ZemanNz/ESP-Demo-Box/documentation/barevny.png

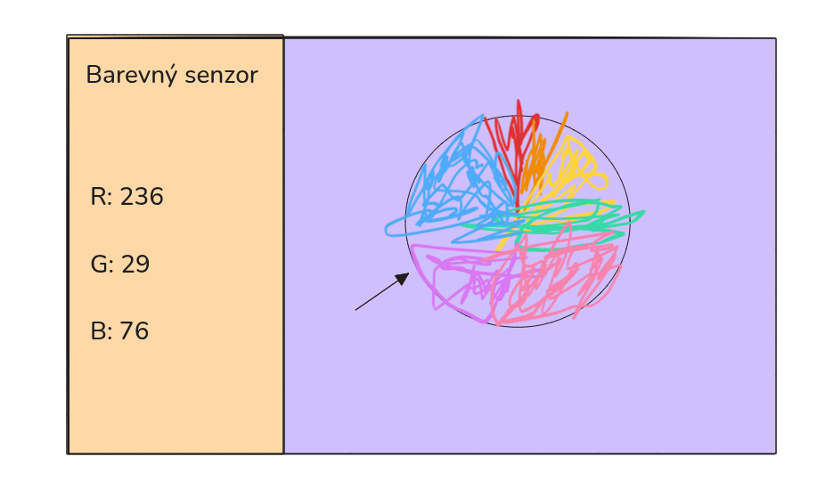
documentation/barevny.png
