ZemanNz/ESP-Demo-Box/documentation/IMG_20260813_224419984.jpg

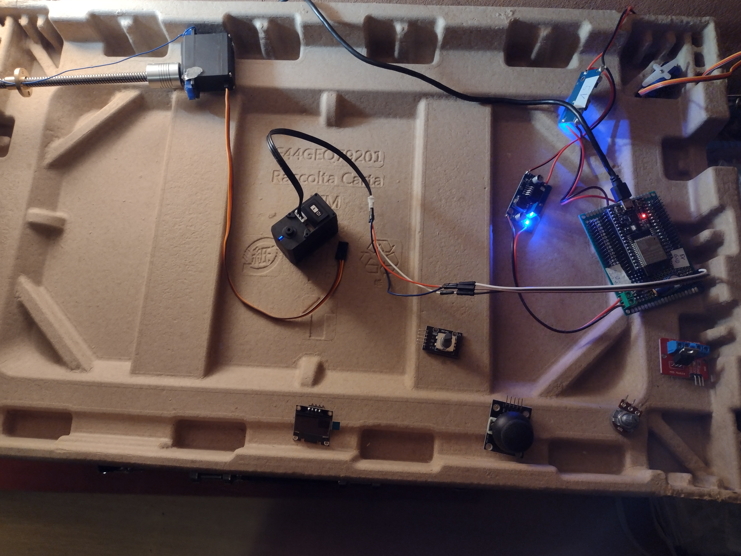
documentation/IMG_20260813_224419984.jpg
