ZemanNz/ESP-Demo-Box/documentation/plan_mode_main_menu.png

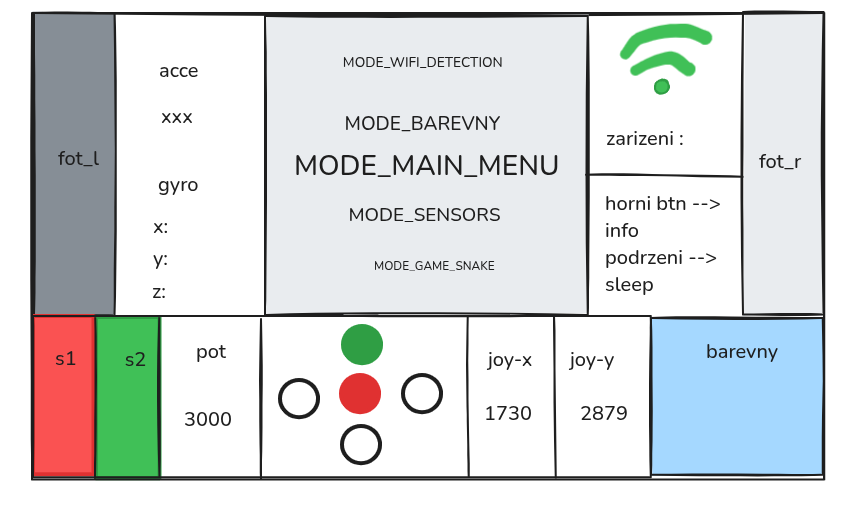
documentation/plan_mode_main_menu.png
