ZemanNz/ESP-Demo-Box/documentation/Snímek obrazovky z 2026-07-06 16-27-45.png

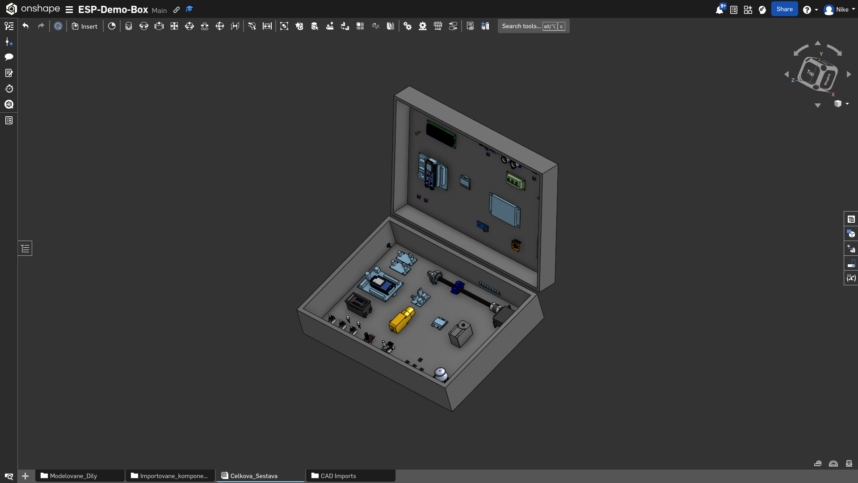
documentation/Snímek obrazovky z 2026-07-06 16-27-45.png
