ZemanNz/ESP-Demo-Box/documentation/Snímek obrazovky z 2026-07-15 17-25-52.png

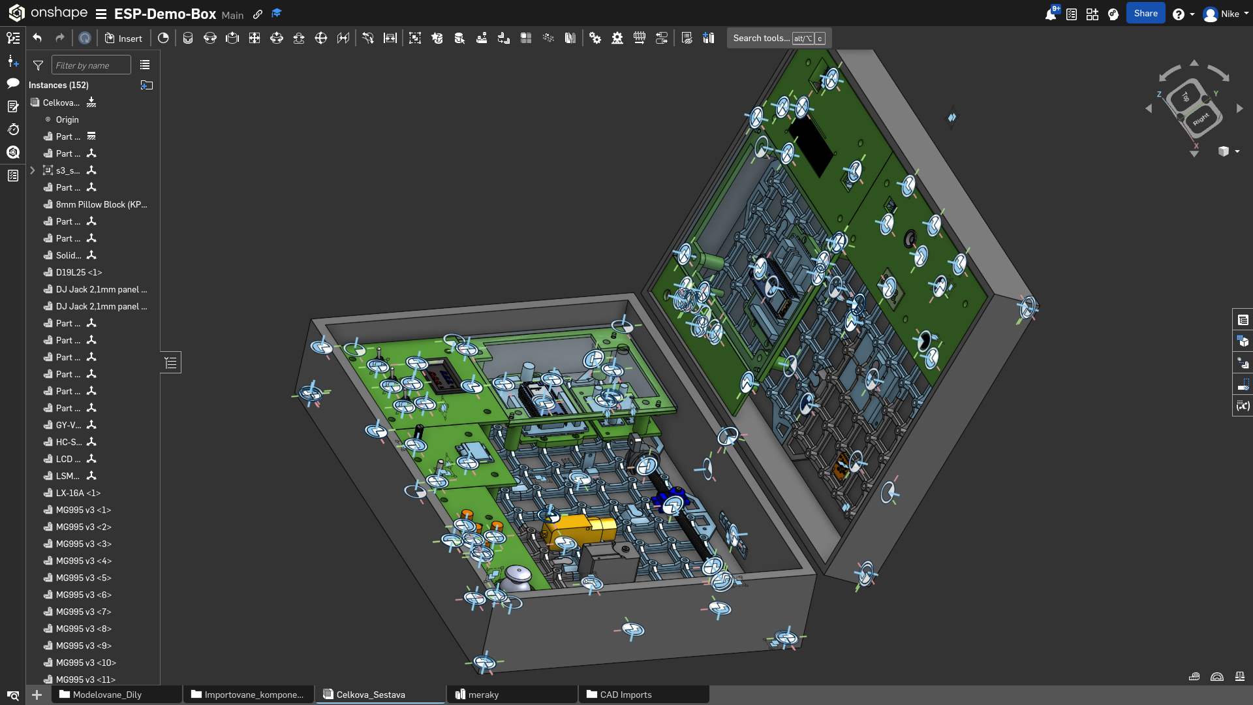
documentation/Snímek obrazovky z 2026-07-15 17-25-52.png
