ZemanNz/ESP-Demo-Box/documentation/Snímek obrazovky z 2026-08-08 21-47-14.png

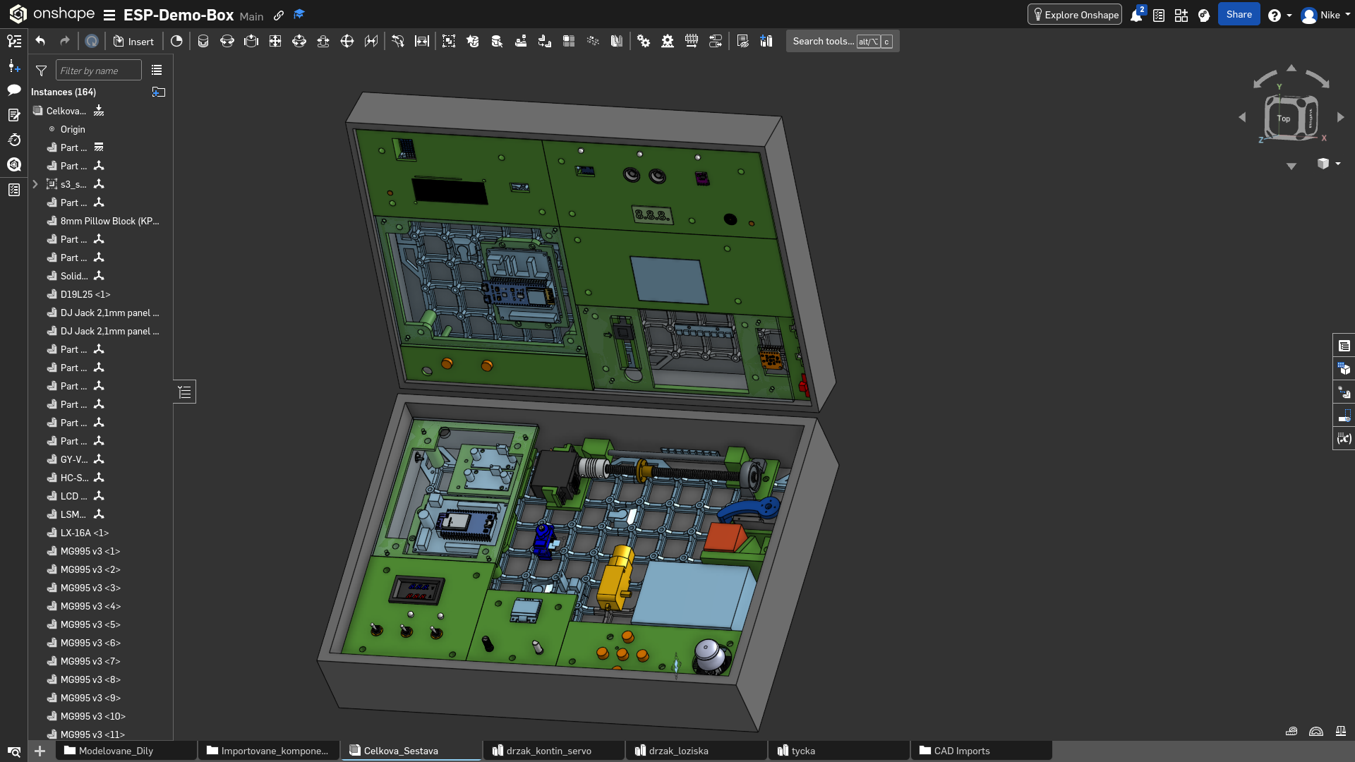
documentation/Snímek obrazovky z 2026-08-08 21-47-14.png
