ZemanNz/ESP-Demo-Box/documentation/Snímek obrazovky z 2026-08-09 14-38-35.png

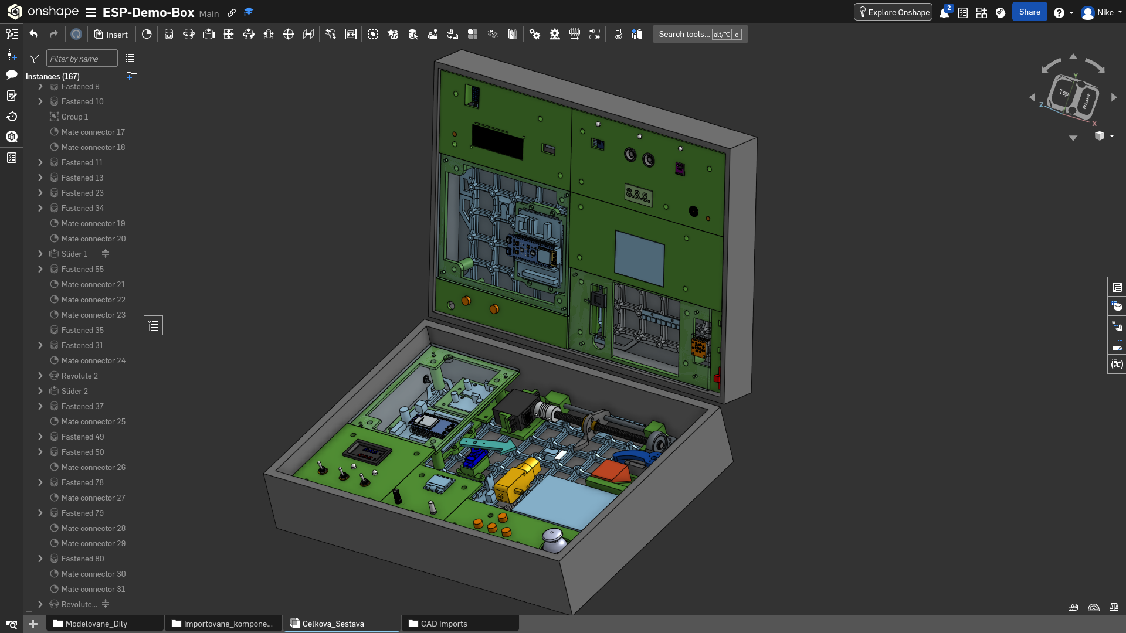
documentation/Snímek obrazovky z 2026-08-09 14-38-35.png
