ZemanNz/ESP-Demo-Box/documentation/vzdalenost.png

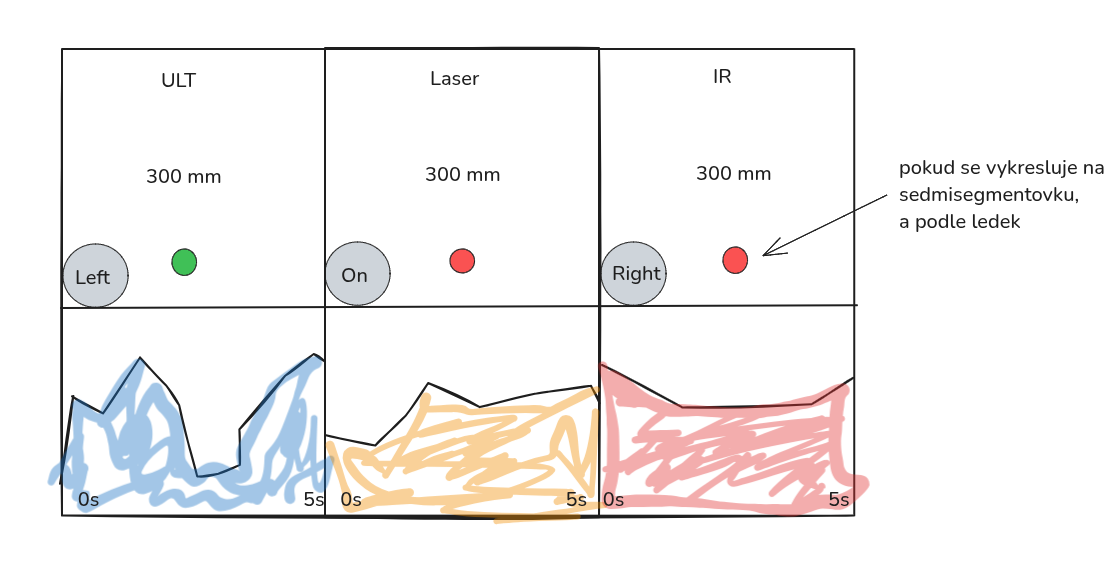
documentation/vzdalenost.png
