ZemanNz/ESP-Demo-Box/documentation/zapojeni_celkem.png

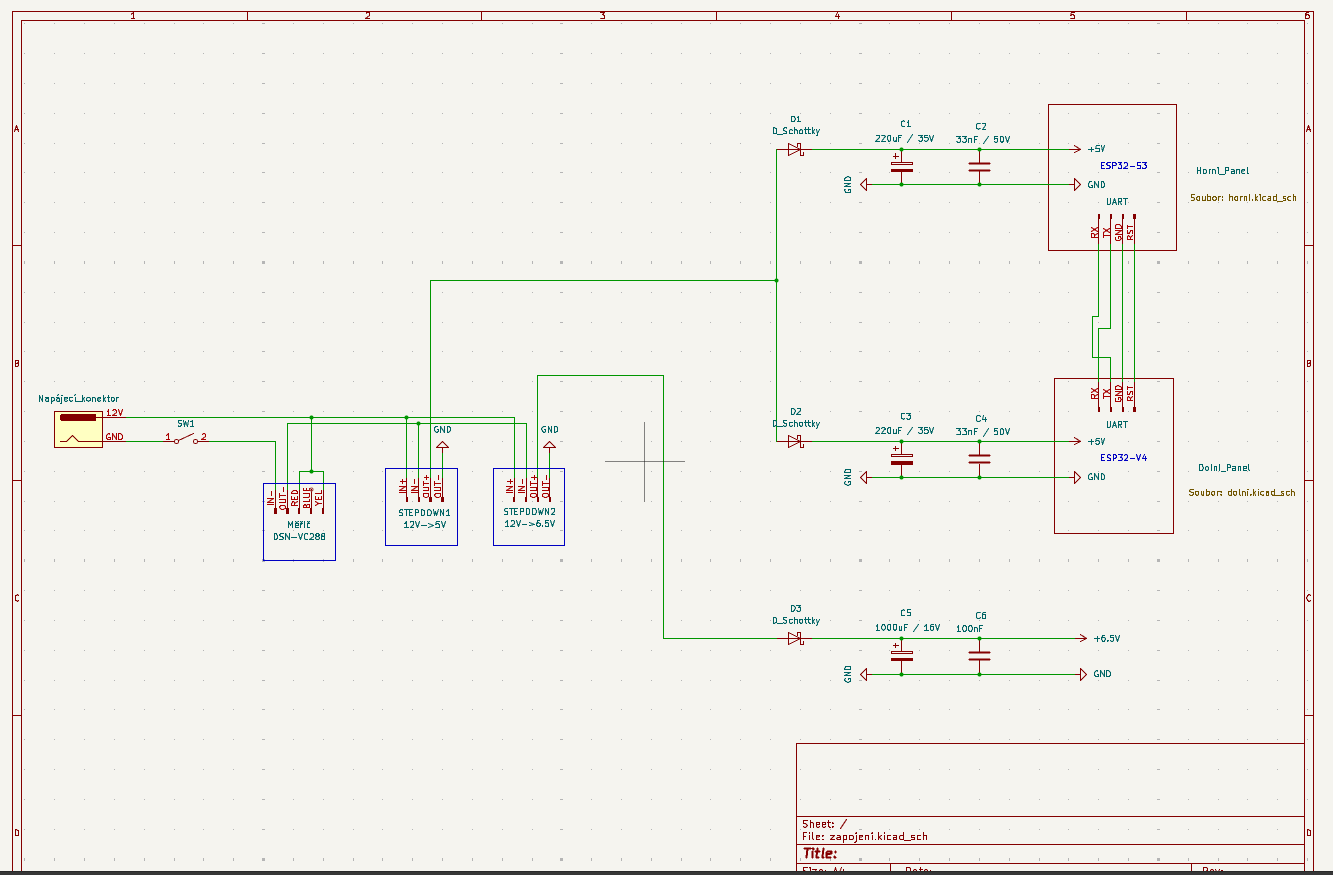
documentation/zapojeni_celkem.png
