ZemanNz/ESP-Demo-Box/documentation/zapojeni_dolni.png

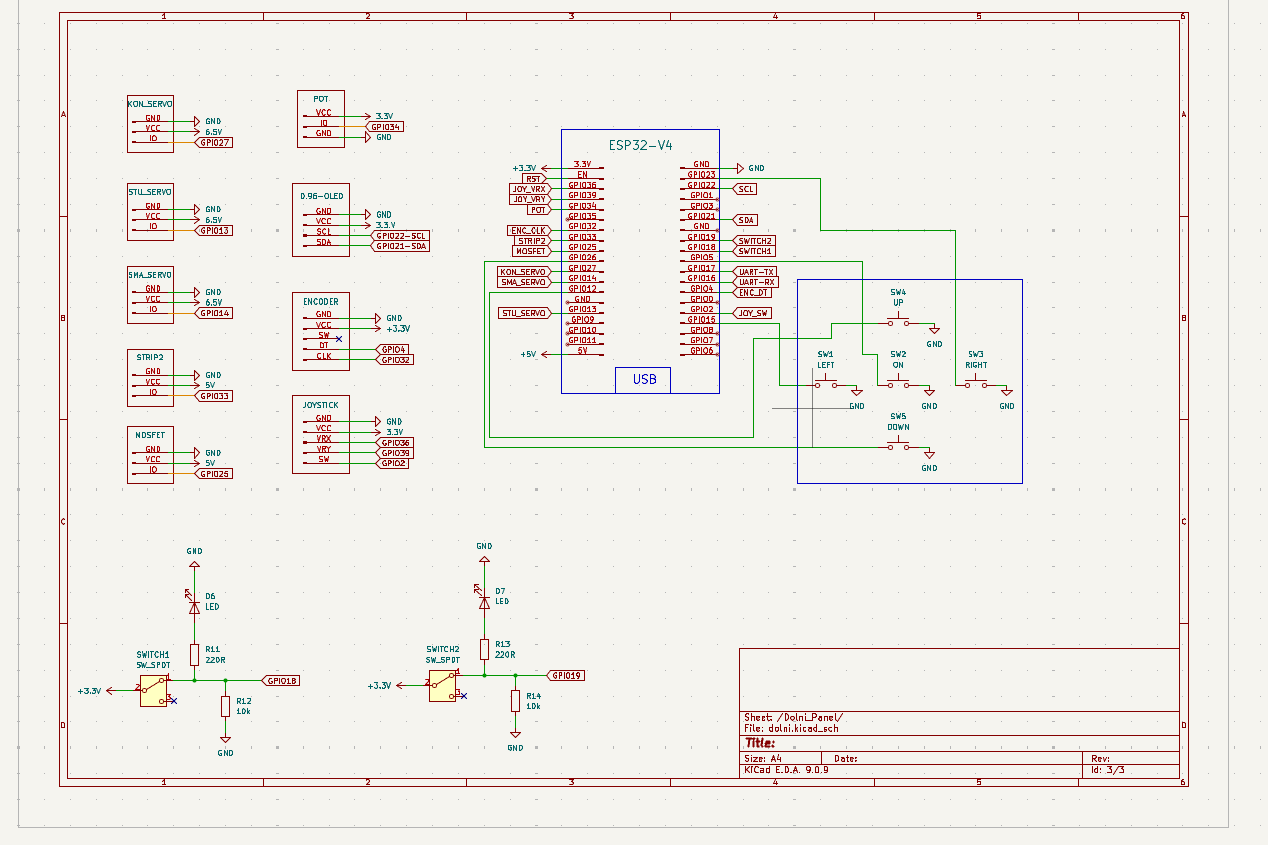
documentation/zapojeni_dolni.png
