ZemanNz/ESP-Demo-Box/hardware/3D/modelovane/drzak_dolni/drzak_dolni_4.step

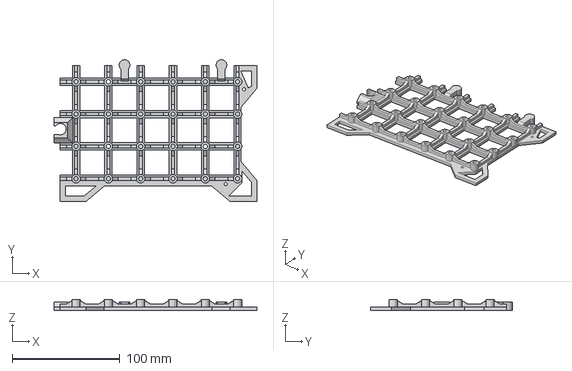
[picture p34: CAD file, 2026-07-23]
hardware/3D/modelovane/drzak_dolni/drzak_dolni_4.step
188.5 x 131.5 x 10.0 mm
