ZemanNz/ESP-Demo-Box/hardware/3D/modelovane/drzak_loziska.step

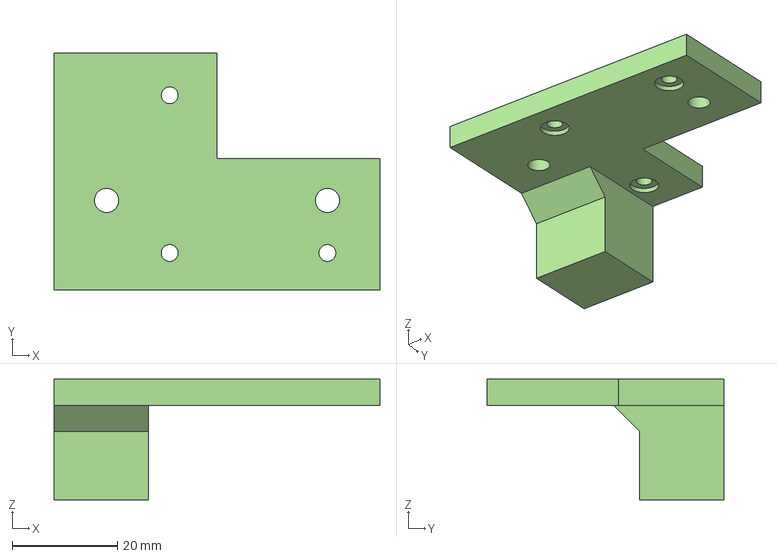
[picture p35: CAD file, 2026-09-20]
hardware/3D/modelovane/drzak_loziska.step
62.0 x 45.0 x 23.0 mm
