ZemanNz/ESP-Demo-Box/hardware/3D/LM2596S_Y000022.step

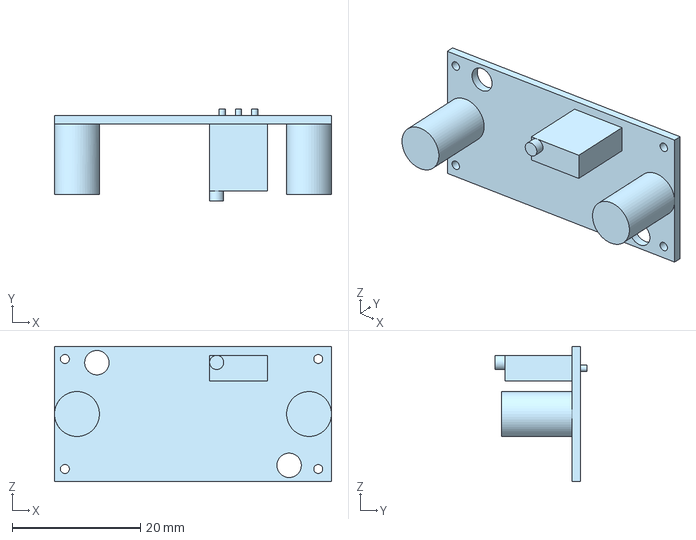
[picture p36: CAD file, 2026-07-23]
hardware/3D/LM2596S_Y000022.step
43.2 x 14.3 x 21.1 mm
