ZemanNz/ESP-Demo-Box/hardware/3D/modelovane/drzak_kontin_servo.step

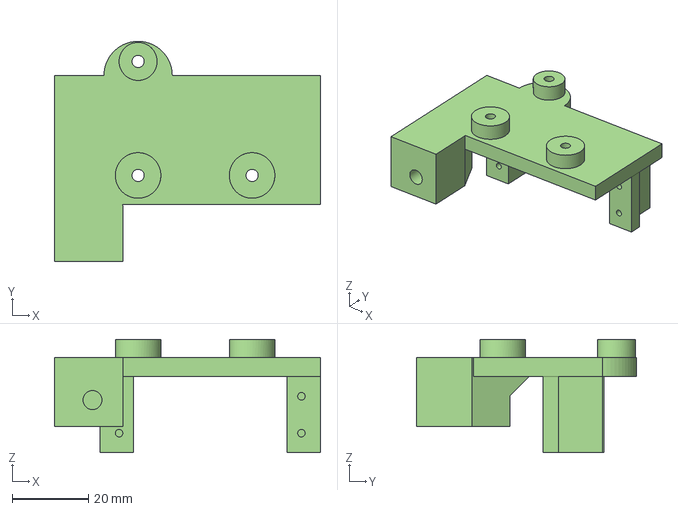
[picture p37: CAD file, 2026-09-20]
hardware/3D/modelovane/drzak_kontin_servo.step
70.0 x 58.0 x 29.9 mm
