ZemanNz/ESP-Demo-Box/hardware/3D/dc 022B jack 2.1mm.step

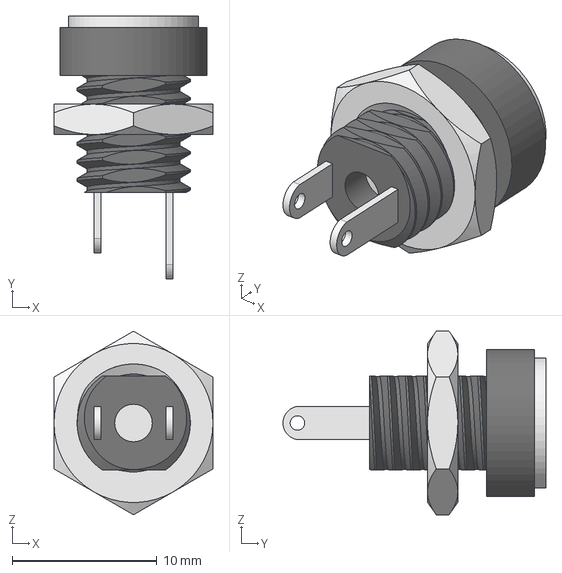
[picture p38: CAD file, 2026-07-23]
hardware/3D/dc 022B jack 2.1mm.step
11.0 x 18.2 x 12.7 mm
