ZemanNz/ESP-Demo-Box/hardware/3D/modelovane/drzak_9g.step

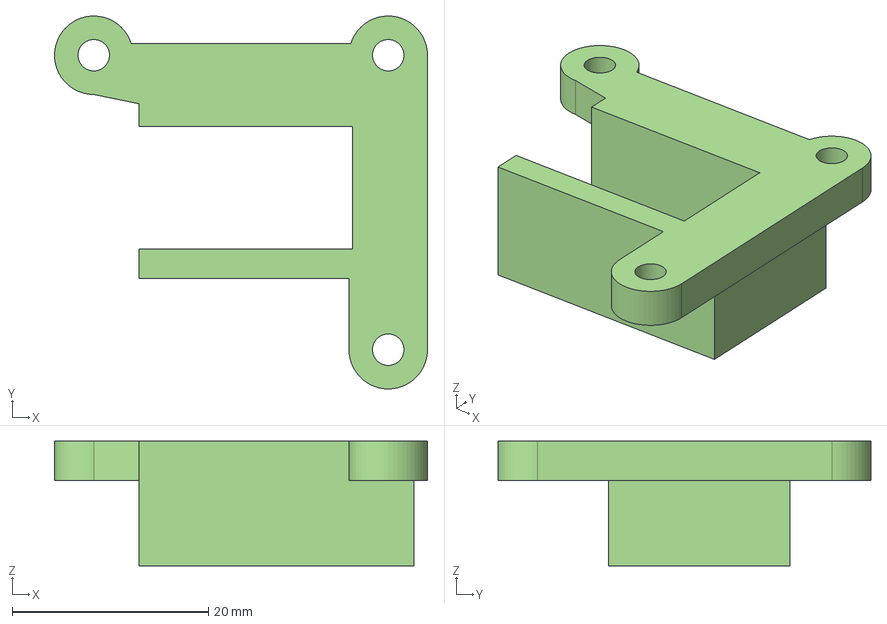
[picture p39: CAD file, 2026-09-20]
hardware/3D/modelovane/drzak_9g.step
38.0 x 38.0 x 12.7 mm
