ZemanNz/ESP-Demo-Box/hardware/3D/modelovane/nad_joy.step

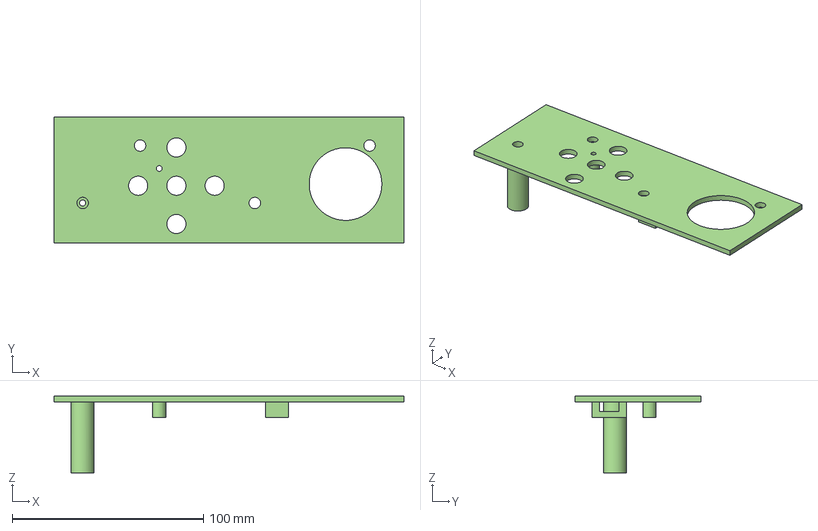
[picture p40: CAD file, 2026-08-15]
hardware/3D/modelovane/nad_joy.step
183.0 x 66.0 x 40.0 mm
