ZemanNz/ESP-Demo-Box/hardware/3D/MTS-102-switch.step

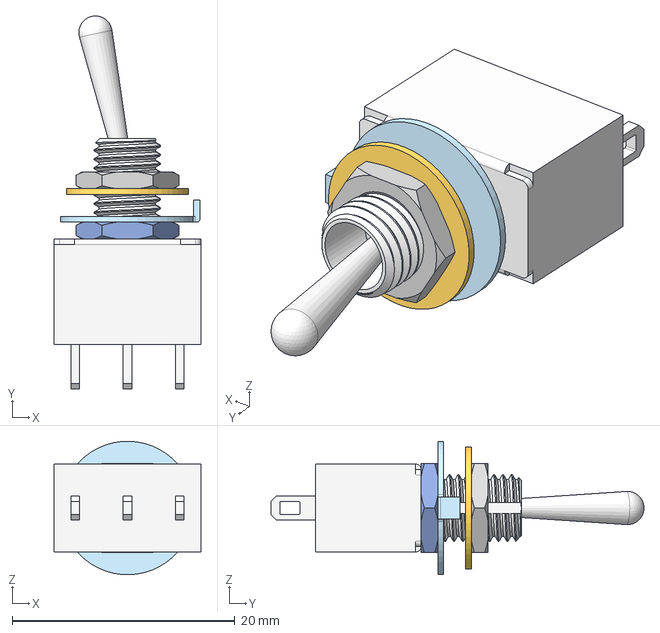
[picture p41: CAD file, 2026-07-23]
hardware/3D/MTS-102-switch.step
13.2 x 33.5 x 12.0 mm
