ZemanNz/ESP-Demo-Box/hardware/3D/modelovane/drzak_joy.step

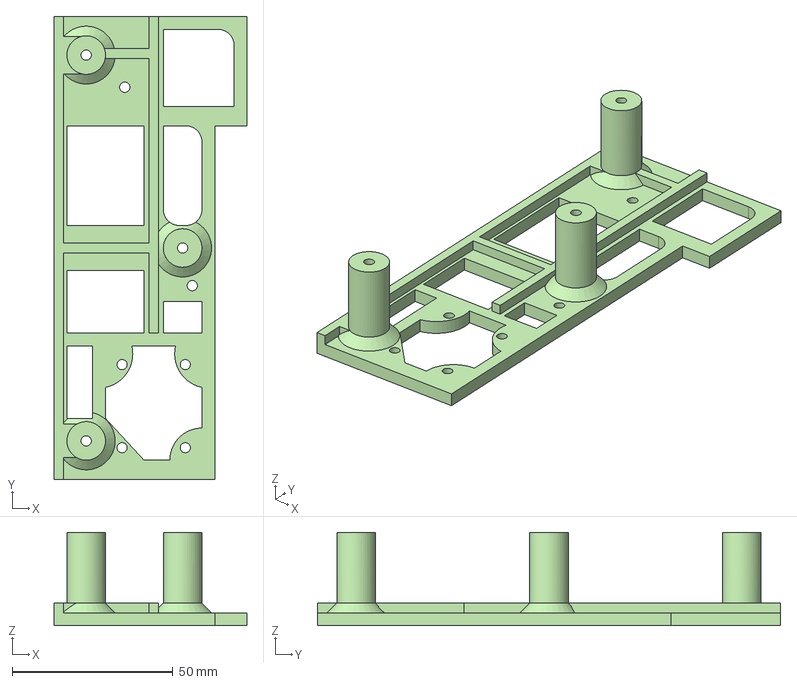
[picture p42: CAD file, 2026-08-15]
hardware/3D/modelovane/drzak_joy.step
60.0 x 144.0 x 29.0 mm
