ZemanNz/ESP-Demo-Box/hardware/3D/HW-040.step

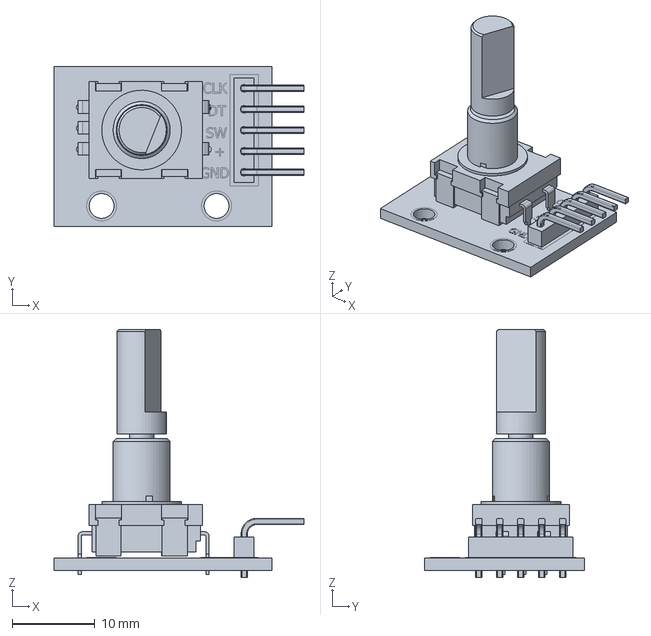
[picture p43: CAD file, 2026-07-23]
hardware/3D/HW-040.step
30.3 x 19.3 x 30.1 mm
