ZemanNz/ESP-Demo-Box/hardware/3D/modelovane/nad_reset.step

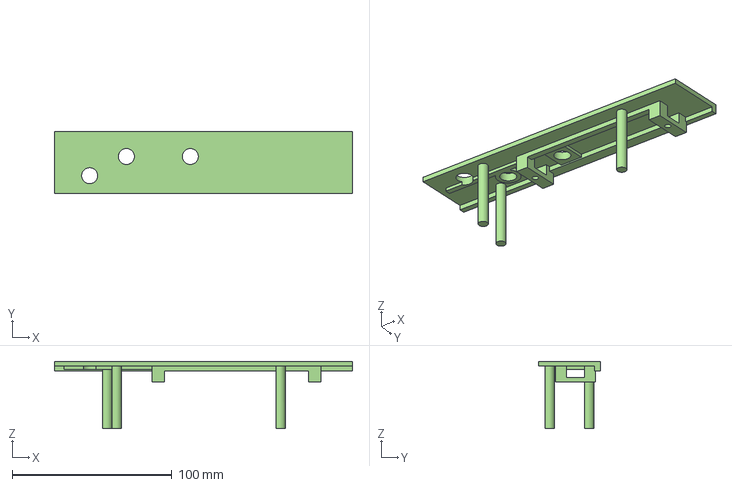
[picture p44: CAD file, 2026-07-23]
hardware/3D/modelovane/nad_reset.step
186.5 x 38.5 x 42.0 mm
