ZemanNz/ESP-Demo-Box/hardware/3D/Joystick Module.step

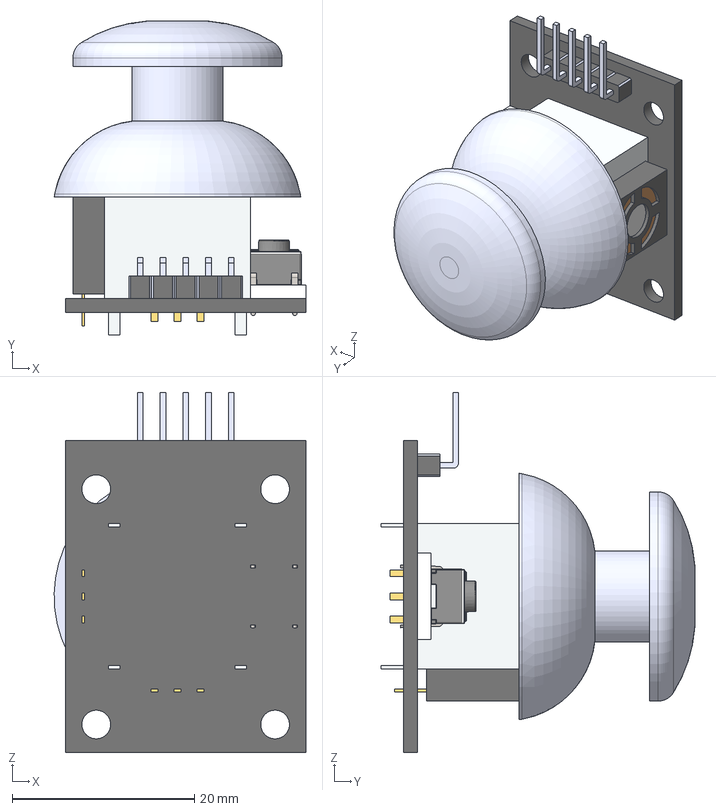
[picture p45: CAD file, 2026-07-23]
hardware/3D/Joystick Module.step
27.6 x 34.5 x 39.5 mm
