ZemanNz/ESP-Demo-Box/hardware/3D/modelovane/drzak_plex_s3.step

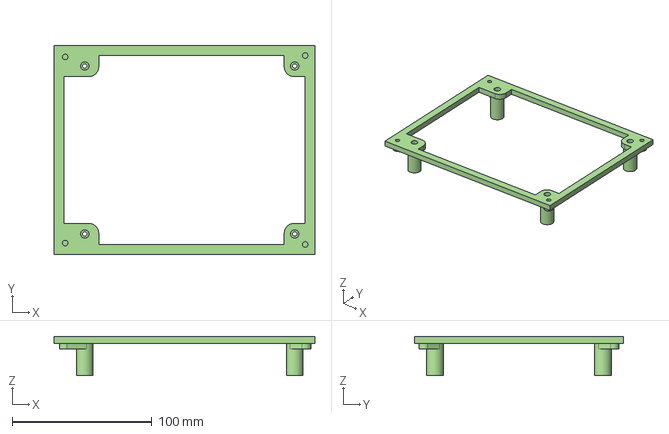
[picture p46: CAD file, 2026-07-23]
hardware/3D/modelovane/drzak_plex_s3.step
186.5 x 149.0 x 28.0 mm
