ZemanNz/ESP-Demo-Box/hardware/3D/DSN-VC288.step

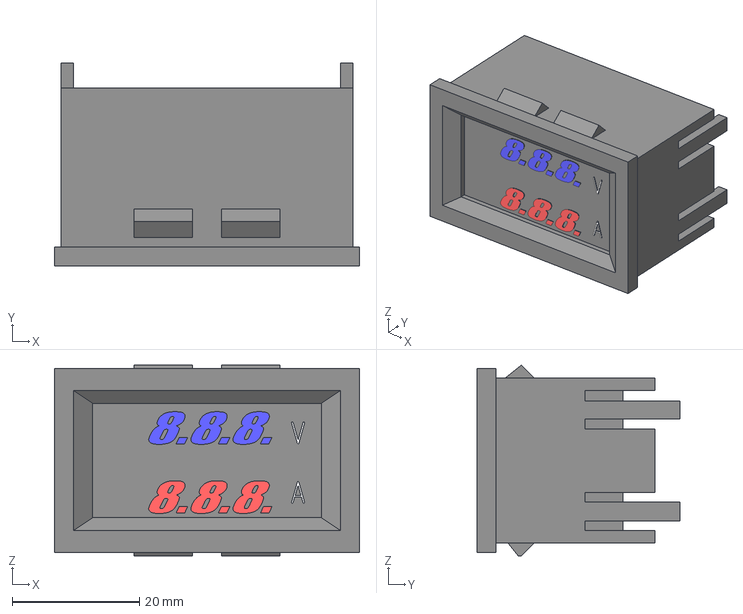
[picture p47: CAD file, 2026-07-23]
hardware/3D/DSN-VC288.step
48.0 x 32.0 x 30.0 mm
