ZemanNz/ESP-Demo-Box/hardware/3D/modelovane/cudlik.step

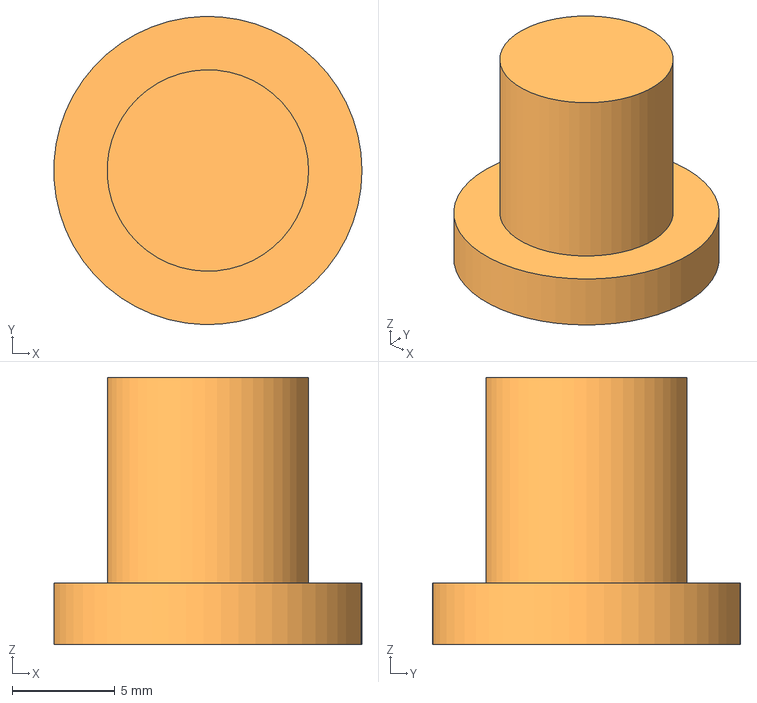
[picture p48: CAD file, 2026-07-23]
hardware/3D/modelovane/cudlik.step
15.0 x 15.0 x 13.0 mm
