ZemanNz/ESP-Demo-Box/hardware/3D/modelovane/barenej_drzak.step

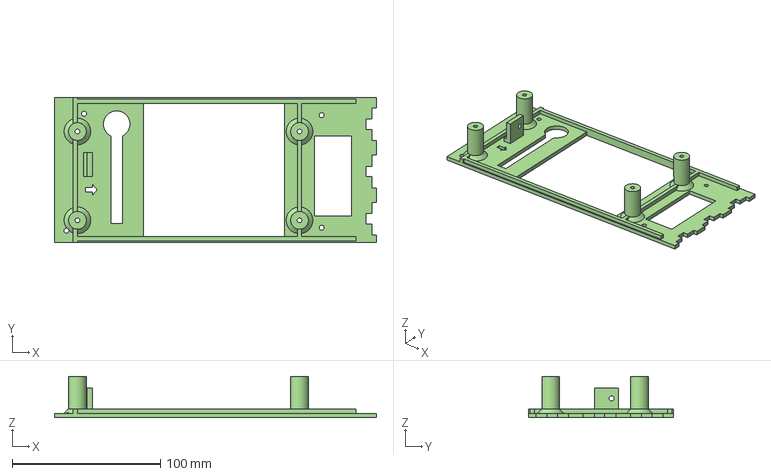
[picture p49: CAD file, 2026-07-23]
hardware/3D/modelovane/barenej_drzak.step
217.5 x 98.0 x 28.0 mm
