ZemanNz/ESP-Demo-Box/hardware/3D/MOS Module.step

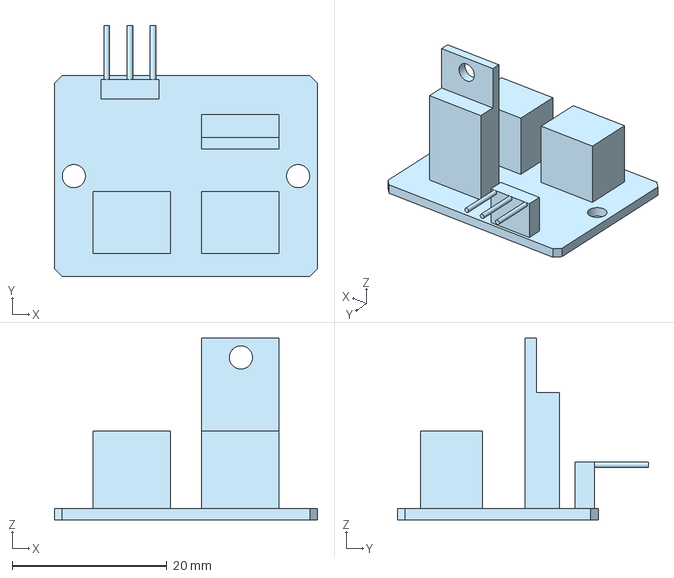
[picture p50: CAD file, 2026-07-23]
hardware/3D/MOS Module.step
34.0 x 32.5 x 23.5 mm
