ZemanNz/ESP-Demo-Box/hardware/3D/GY-VL53LDK.step

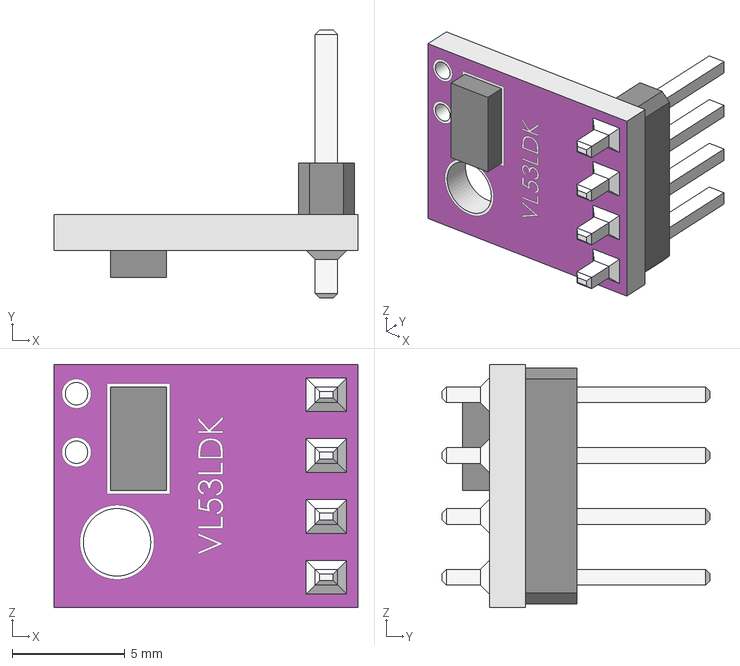
[picture p51: CAD file, 2026-07-23]
hardware/3D/GY-VL53LDK.step
13.5 x 11.9 x 10.8 mm
