ZemanNz/ESP-Demo-Box/hardware/3D/modelovane/drzak_switch.step

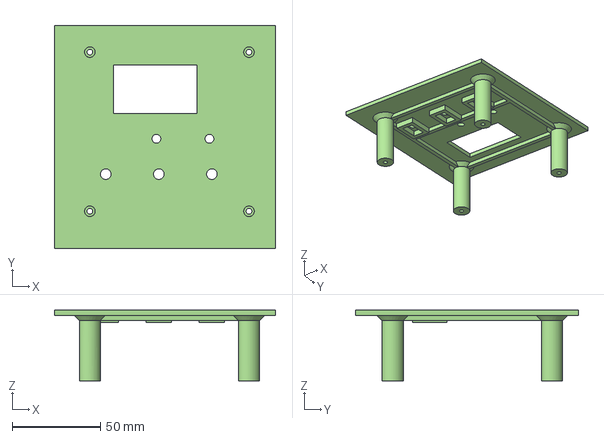
[picture p52: CAD file, 2026-07-23]
hardware/3D/modelovane/drzak_switch.step
125.0 x 126.0 x 40.0 mm
