ZemanNz/ESP-Demo-Box/hardware/3D/HC-SR04.step

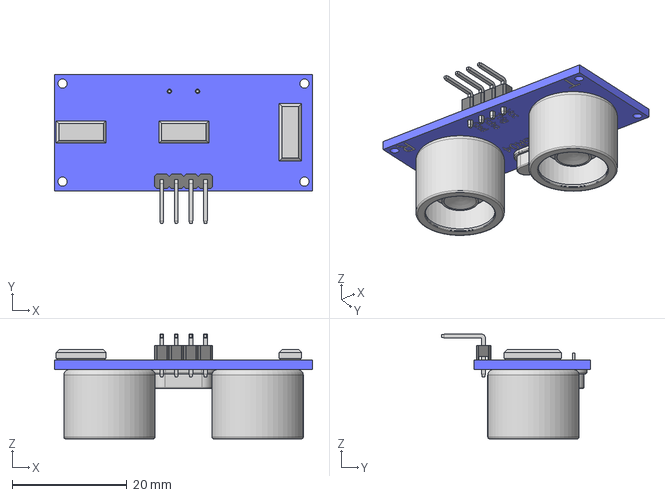
[picture p53: CAD file, 2026-07-23]
hardware/3D/HC-SR04.step
45.0 x 26.0 x 18.3 mm
