ZemanNz/ESP-Demo-Box/hardware/3D/modelovane/drzak_pot.step

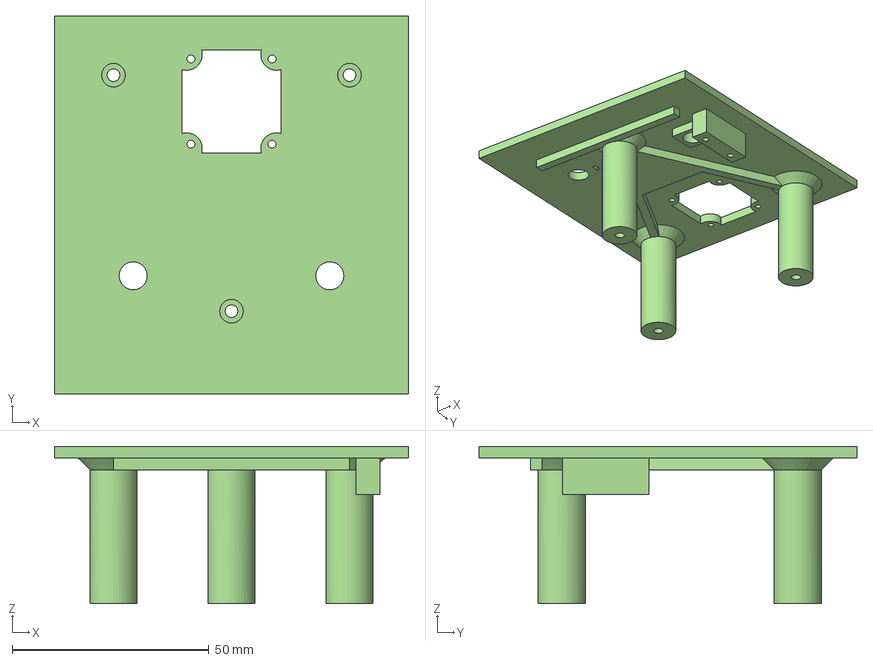
[picture p54: CAD file, 2026-07-23]
hardware/3D/modelovane/drzak_pot.step
90.0 x 96.0 x 40.0 mm
