ZemanNz/ESP-Demo-Box/hardware/3D/Led 5mm - white.step

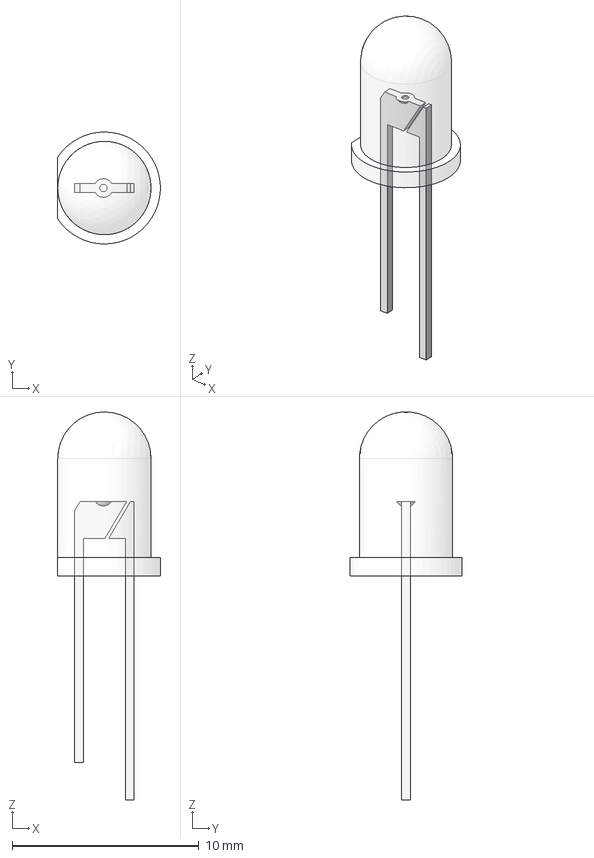
[picture p55: CAD file, 2026-07-23]
hardware/3D/Led 5mm - white.step
5.49 x 6.00 x 20.8 mm
