ZemanNz/ESP-Demo-Box/hardware/3D/modelovane/lcd_gyro_drz.step

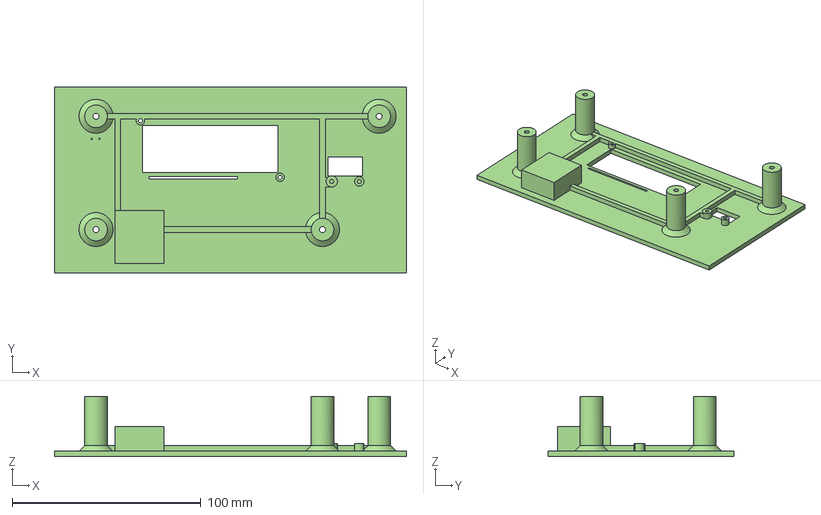
[picture p56: CAD file, 2026-07-23]
hardware/3D/modelovane/lcd_gyro_drz.step
186.5 x 98.5 x 32.0 mm
