ZemanNz/ESP-Demo-Box/hardware/3D/LSM6DS3.step

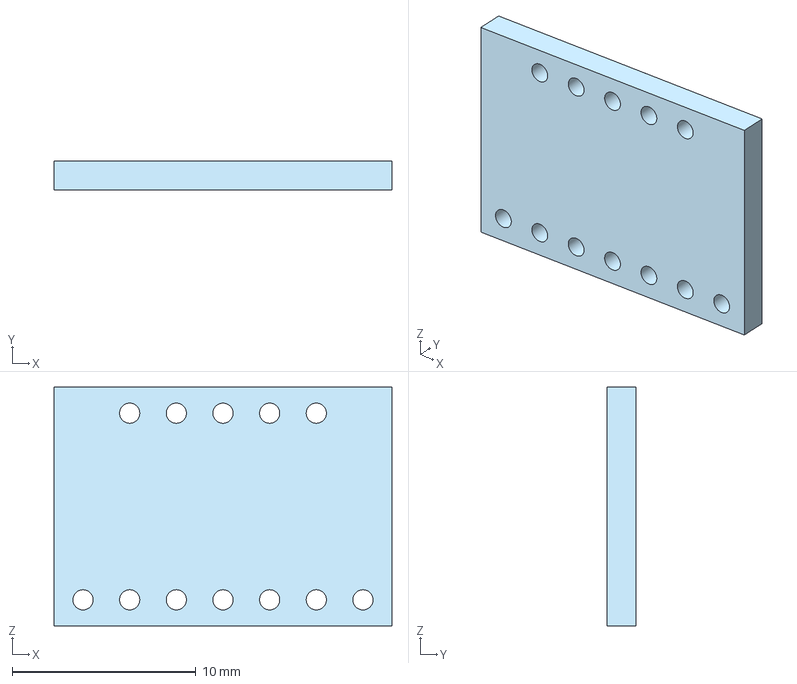
[picture p57: CAD file, 2026-07-23]
hardware/3D/LSM6DS3.step
18.4 x 1.60 x 13.0 mm
