ZemanNz/ESP-Demo-Box/hardware/3D/modelovane/drzak_s3.step

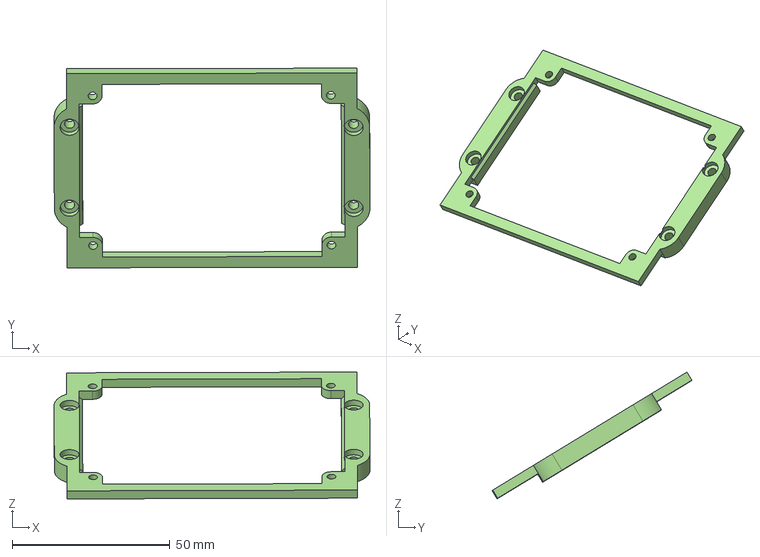
[picture p58: CAD file, 2026-07-23]
hardware/3D/modelovane/drzak_s3.step
100.1 x 63.3 x 40.2 mm
