ZemanNz/ESP-Demo-Box/hardware/3D/28BYJ-48.step

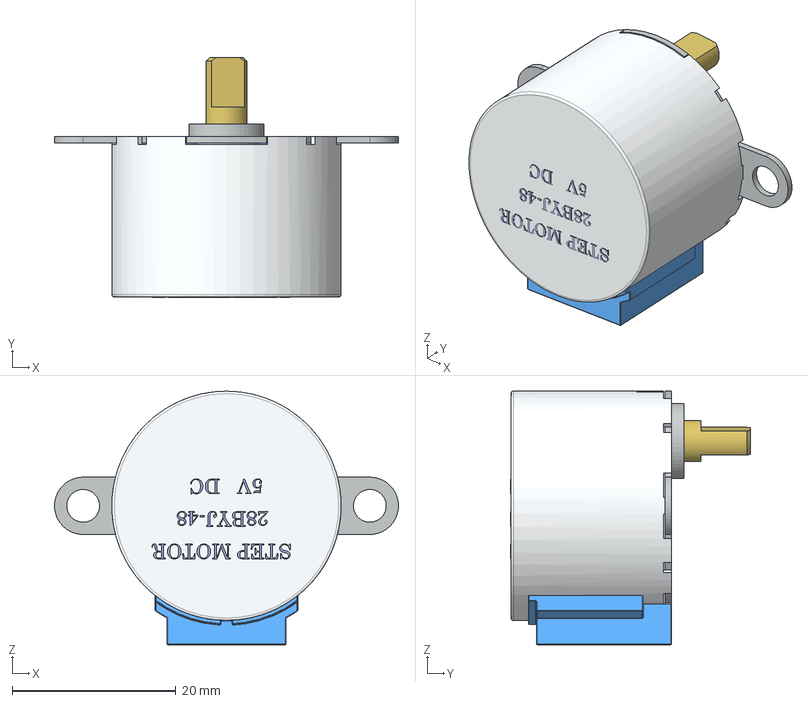
[picture p59: CAD file, 2026-07-23]
hardware/3D/28BYJ-48.step
42.0 x 29.3 x 31.0 mm
28BYJ-48-005
28BYJ-48-002
28BYJ-48-003
28BYJ-48-006
Stepper Motor
