ZemanNz/ESP-Demo-Box/hardware/3D/modelovane/drzak_2.8_display.step

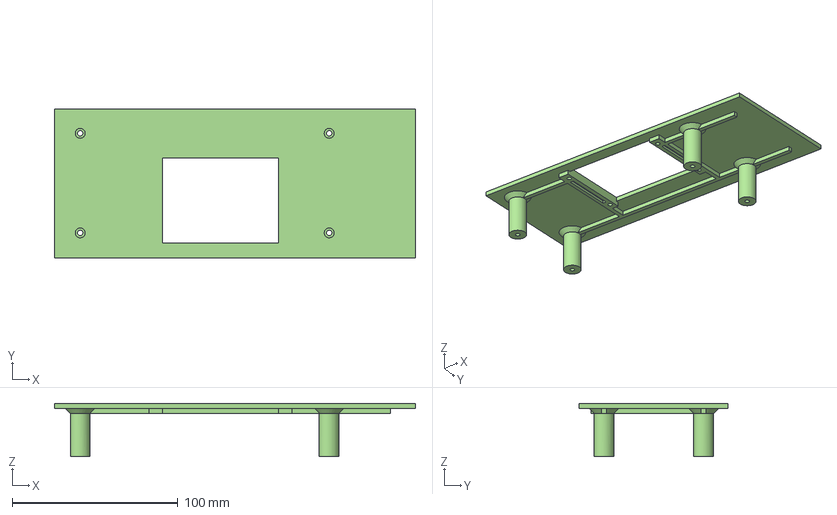
[picture p60: CAD file, 2026-07-23]
hardware/3D/modelovane/drzak_2.8_display.step
217.5 x 89.5 x 32.0 mm
