ZemanNz/ESP-Demo-Box/hardware/3D/modelovane/stepdown_drzak.step

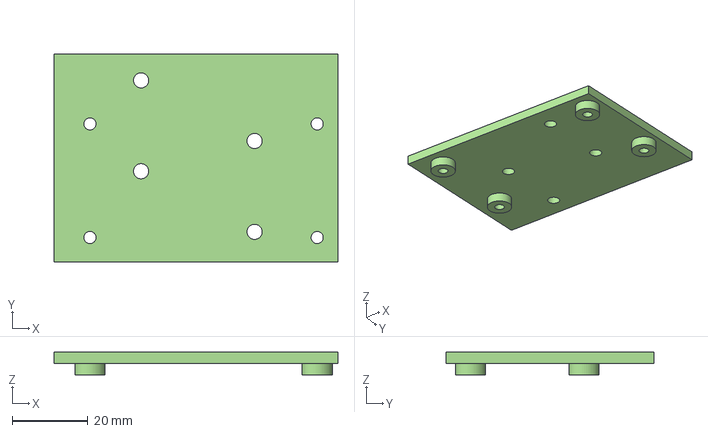
[picture p61: CAD file, 2026-07-23]
hardware/3D/modelovane/stepdown_drzak.step
75.0 x 55.0 x 6.00 mm
