ZemanNz/ESP-Demo-Box/hardware/3D/modelovane/drzak_plex_dole.step

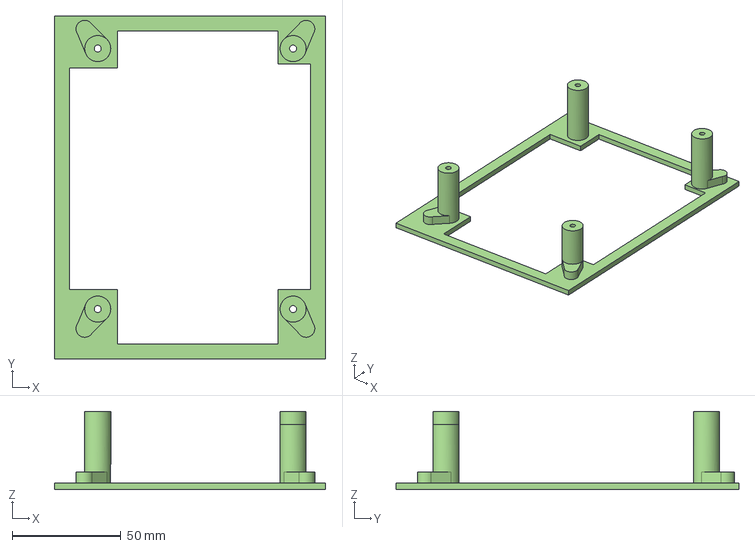
[picture p62: CAD file, 2026-07-23]
hardware/3D/modelovane/drzak_plex_dole.step
125.0 x 158.0 x 36.0 mm
