ZemanNz/ESP-Demo-Box/hardware/3D/2.8- Display.step

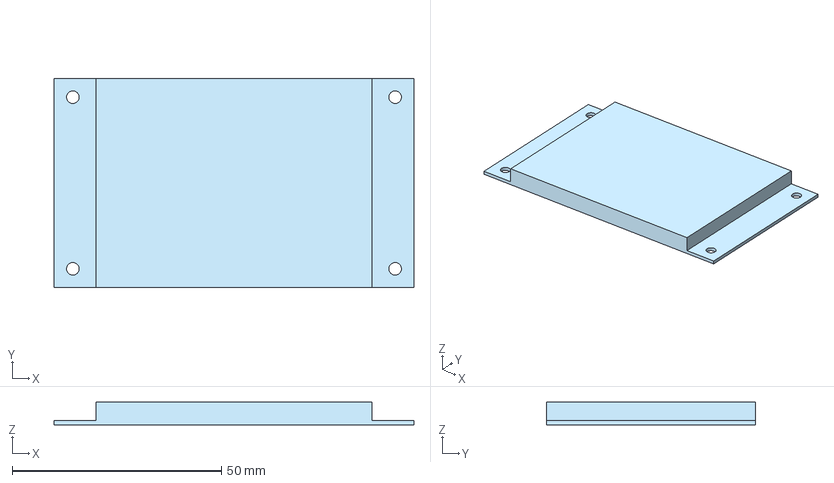
[picture p63: CAD file, 2026-07-23]
hardware/3D/2.8- Display.step
86.0 x 50.0 x 5.40 mm
