ZemanNz/ESP-Demo-Box/hardware/3D/modelovane/plexisklo_s3.step

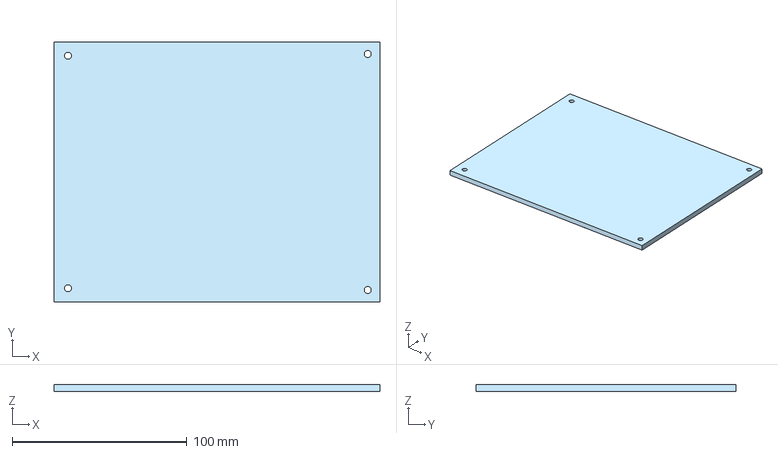
[picture p64: CAD file, 2026-07-23]
hardware/3D/modelovane/plexisklo_s3.step
186.5 x 149.0 x 4.00 mm
