ZemanNz/ESP-Demo-Box/hardware/3D/modelovane/meraky.step

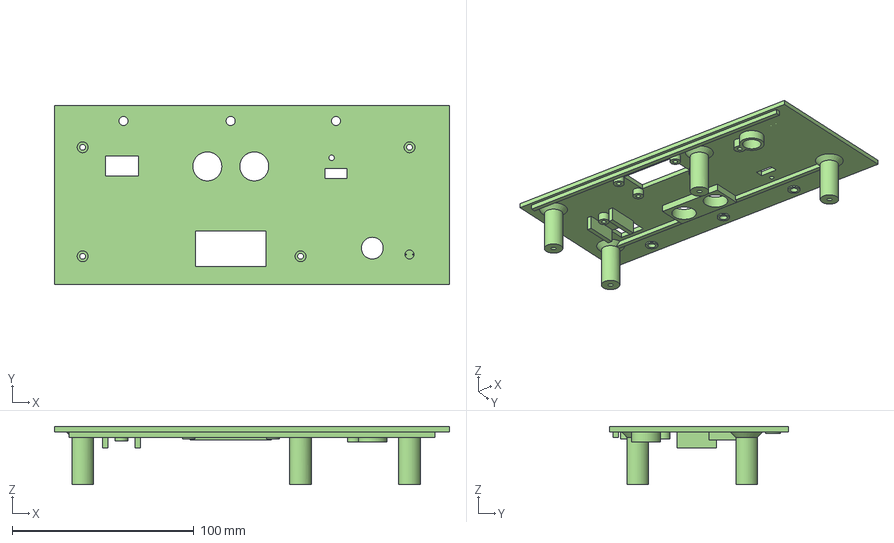
[picture p65: CAD file, 2026-07-23]
hardware/3D/modelovane/meraky.step
217.5 x 98.5 x 32.0 mm
