ZemanNz/ESP-Demo-Box/hardware/3D/ws2812b led strip.step

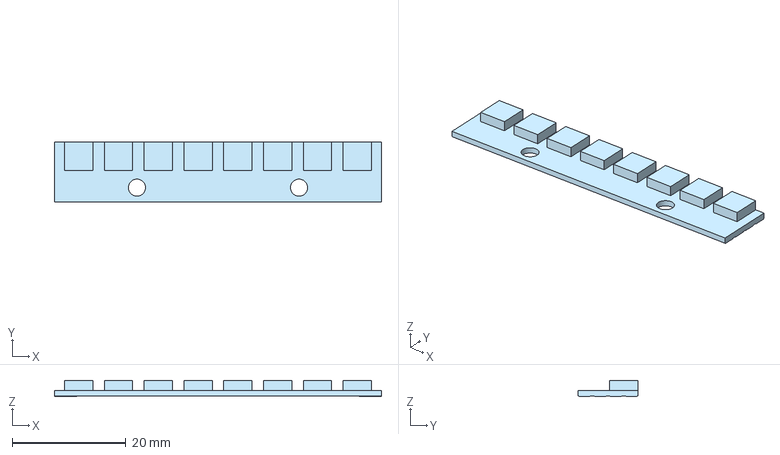
[picture p66: CAD file, 2026-07-23]
hardware/3D/ws2812b led strip.step
57.5 x 10.5 x 2.85 mm
