ZemanNz/ESP-Demo-Box/hardware/3D/LX-16A.step

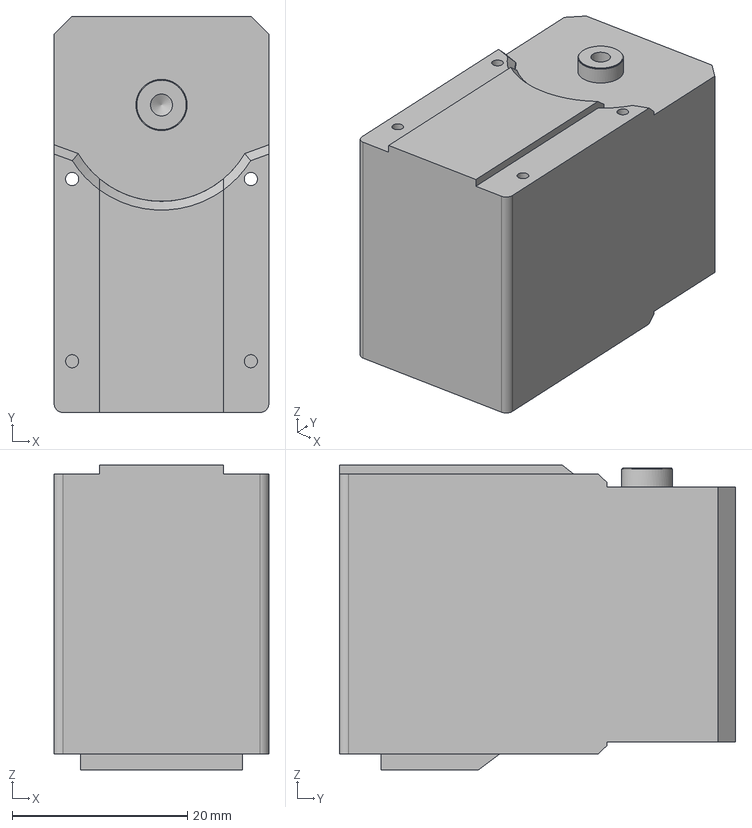
[picture p67: CAD file, 2026-07-23]
hardware/3D/LX-16A.step
24.5 x 45.2 x 34.8 mm
