ZemanNz/ESP-Demo-Box/hardware/3D/modelovane/01_test.step

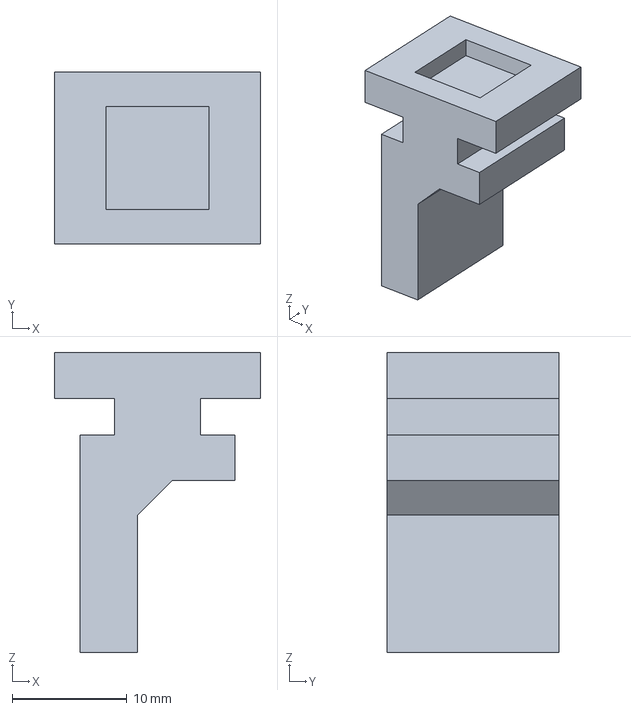
[picture p68: CAD file, 2026-07-23]
hardware/3D/modelovane/01_test.step
18.0 x 15.0 x 26.2 mm
