ZemanNz/ESP-Demo-Box/hardware/3D/modelovane/reset_tlac_drzak.step

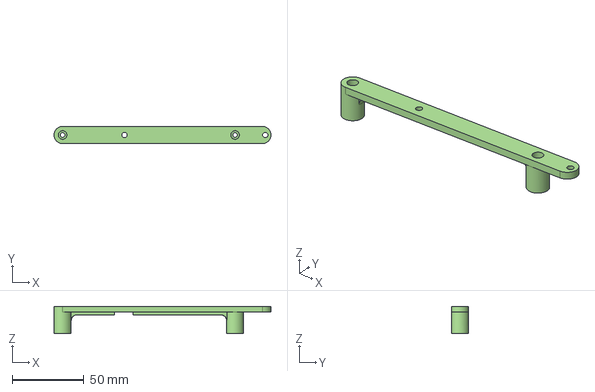
[picture p69: CAD file, 2026-07-23]
hardware/3D/modelovane/reset_tlac_drzak.step
151.0 x 12.0 x 19.0 mm
