ZemanNz/ESP-Demo-Box/hardware/3D/potenciometar.step

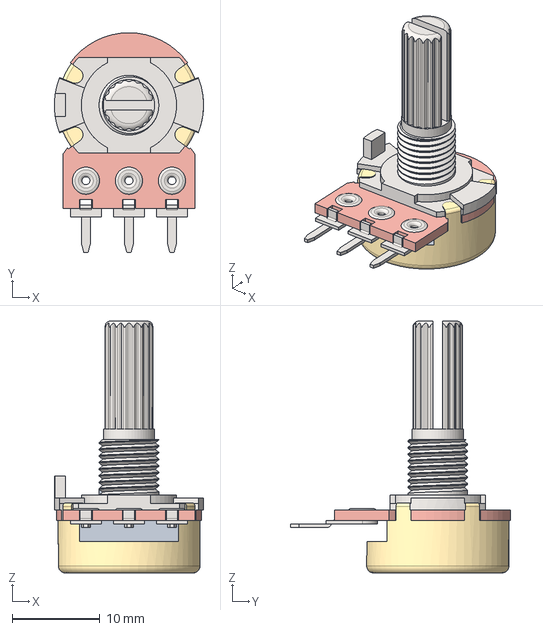
[picture p70: CAD file, 2026-07-23]
hardware/3D/potenciometar.step
17.0 x 25.0 x 28.7 mm
