ZemanNz/ESP-Demo-Box/hardware/3D/dc motor(2).step

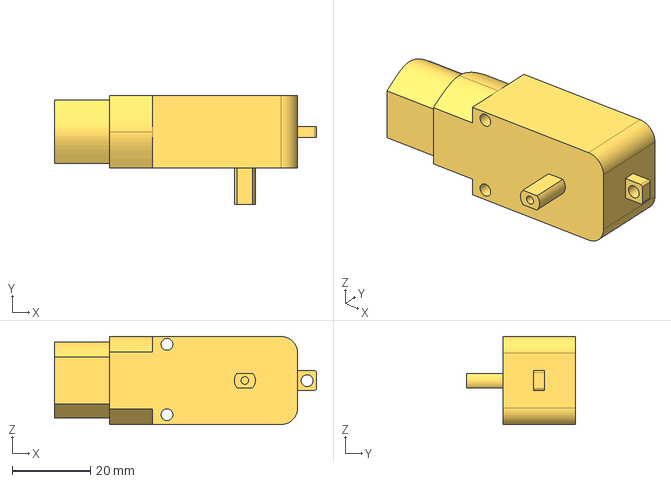
[picture p71: CAD file, 2026-07-23]
hardware/3D/dc motor(2).step
66.8 x 27.9 x 22.4 mm
