ZemanNz/ESP-Demo-Box/hardware/3D/MG995.step

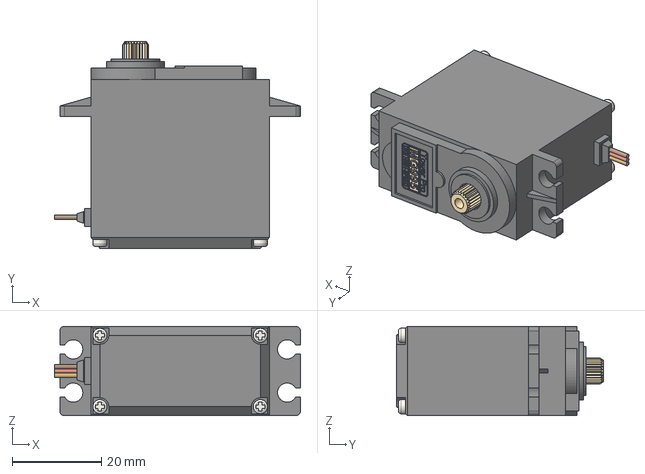
[picture p72: CAD file, 2026-07-23]
hardware/3D/MG995.step
55.2 x 46.5 x 20.0 mm
