ZemanNz/ESP-Demo-Box/hardware/3D/LCD 1602.step

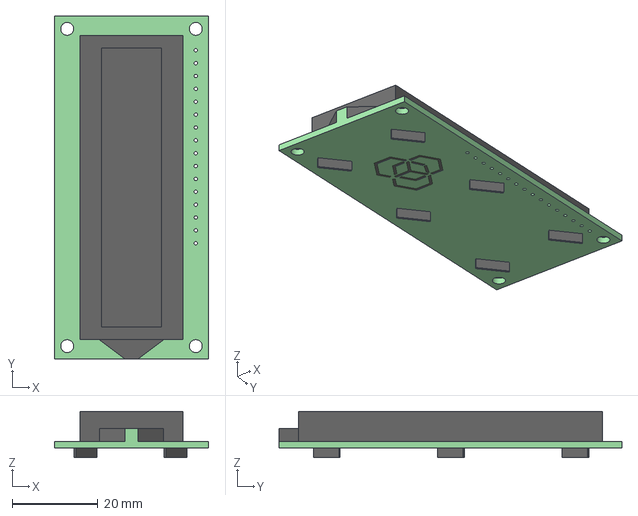
[picture p73: CAD file, 2026-07-23]
hardware/3D/LCD 1602.step
36.0 x 80.0 x 10.8 mm
