ZemanNz/ESP-Demo-Box/hardware/3D/Buzzer Module - FC-07 - PCB.step

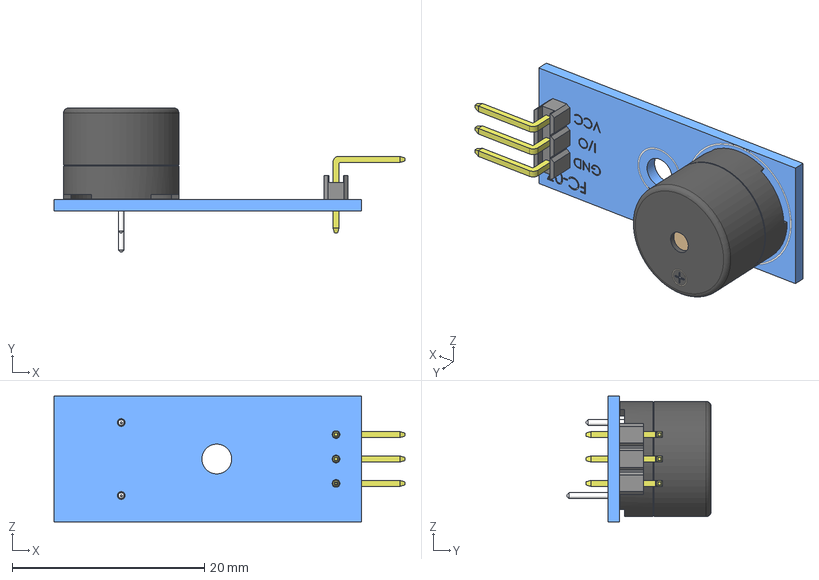
[picture p74: CAD file, 2026-07-23]
hardware/3D/Buzzer Module - FC-07 - PCB.step
36.5 x 15.0 x 13.1 mm
