ZemanNz/ESP-Demo-Box/hardware/3D/8mm Pillow Block (KP08).step

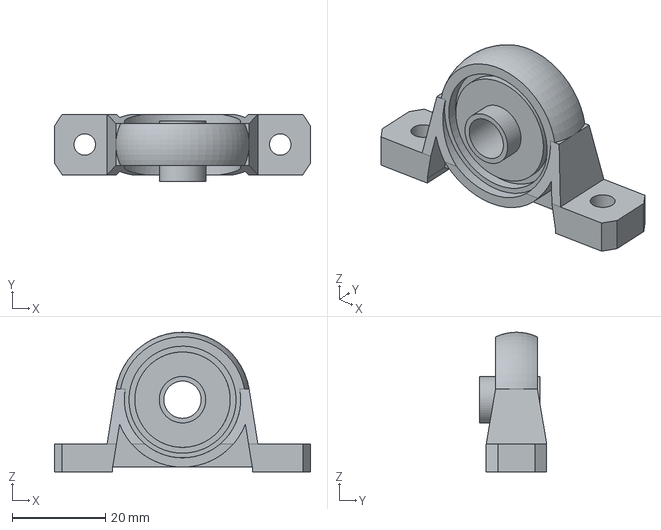
[picture p75: CAD file, 2026-07-23]
hardware/3D/8mm Pillow Block (KP08).step
55.0 x 14.5 x 30.0 mm
