ZemanNz/ESP-Demo-Box/hardware/3D/MODULO SENSOR OPTICO MH.step

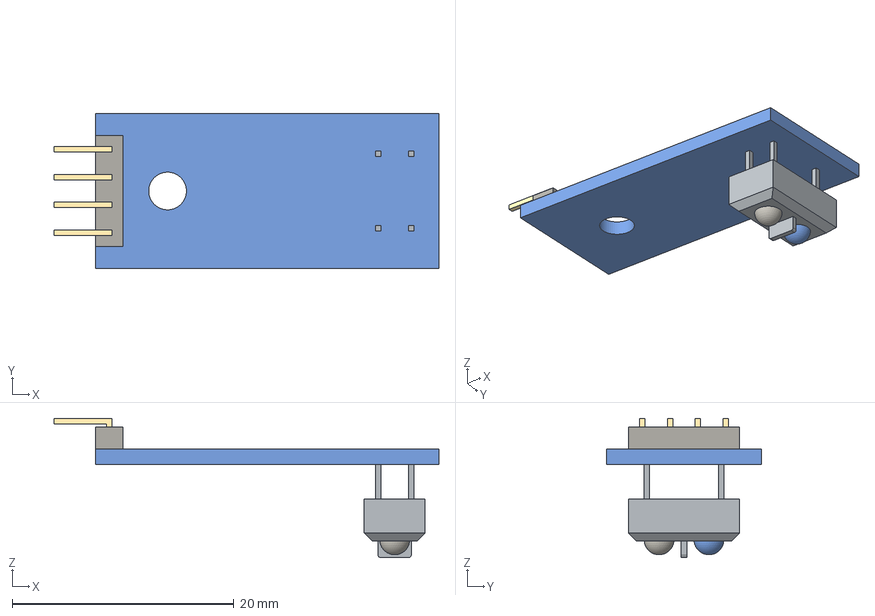
[picture p76: CAD file, 2026-07-23]
hardware/3D/MODULO SENSOR OPTICO MH.step
34.8 x 14.0 x 12.5 mm
