ZemanNz/ESP-Demo-Box/hardware/3D/OLED 0.96.step

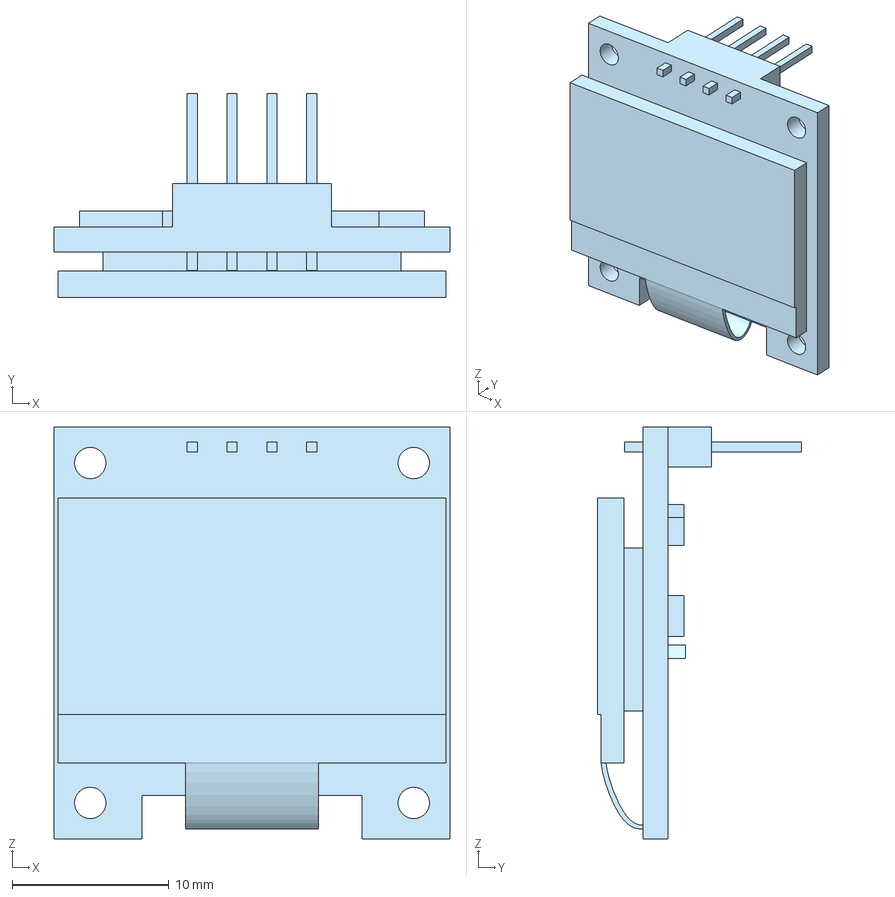
[picture p77: CAD file, 2026-07-23]
hardware/3D/OLED 0.96.step
25.2 x 13.0 x 26.3 mm
