ZemanNz/ESP-Demo-Box/documentation/zapojeni/dolni.kicad_sch

## KiCad design documentation/zapojeni/dolni.kicad_sch (2026-09-20)

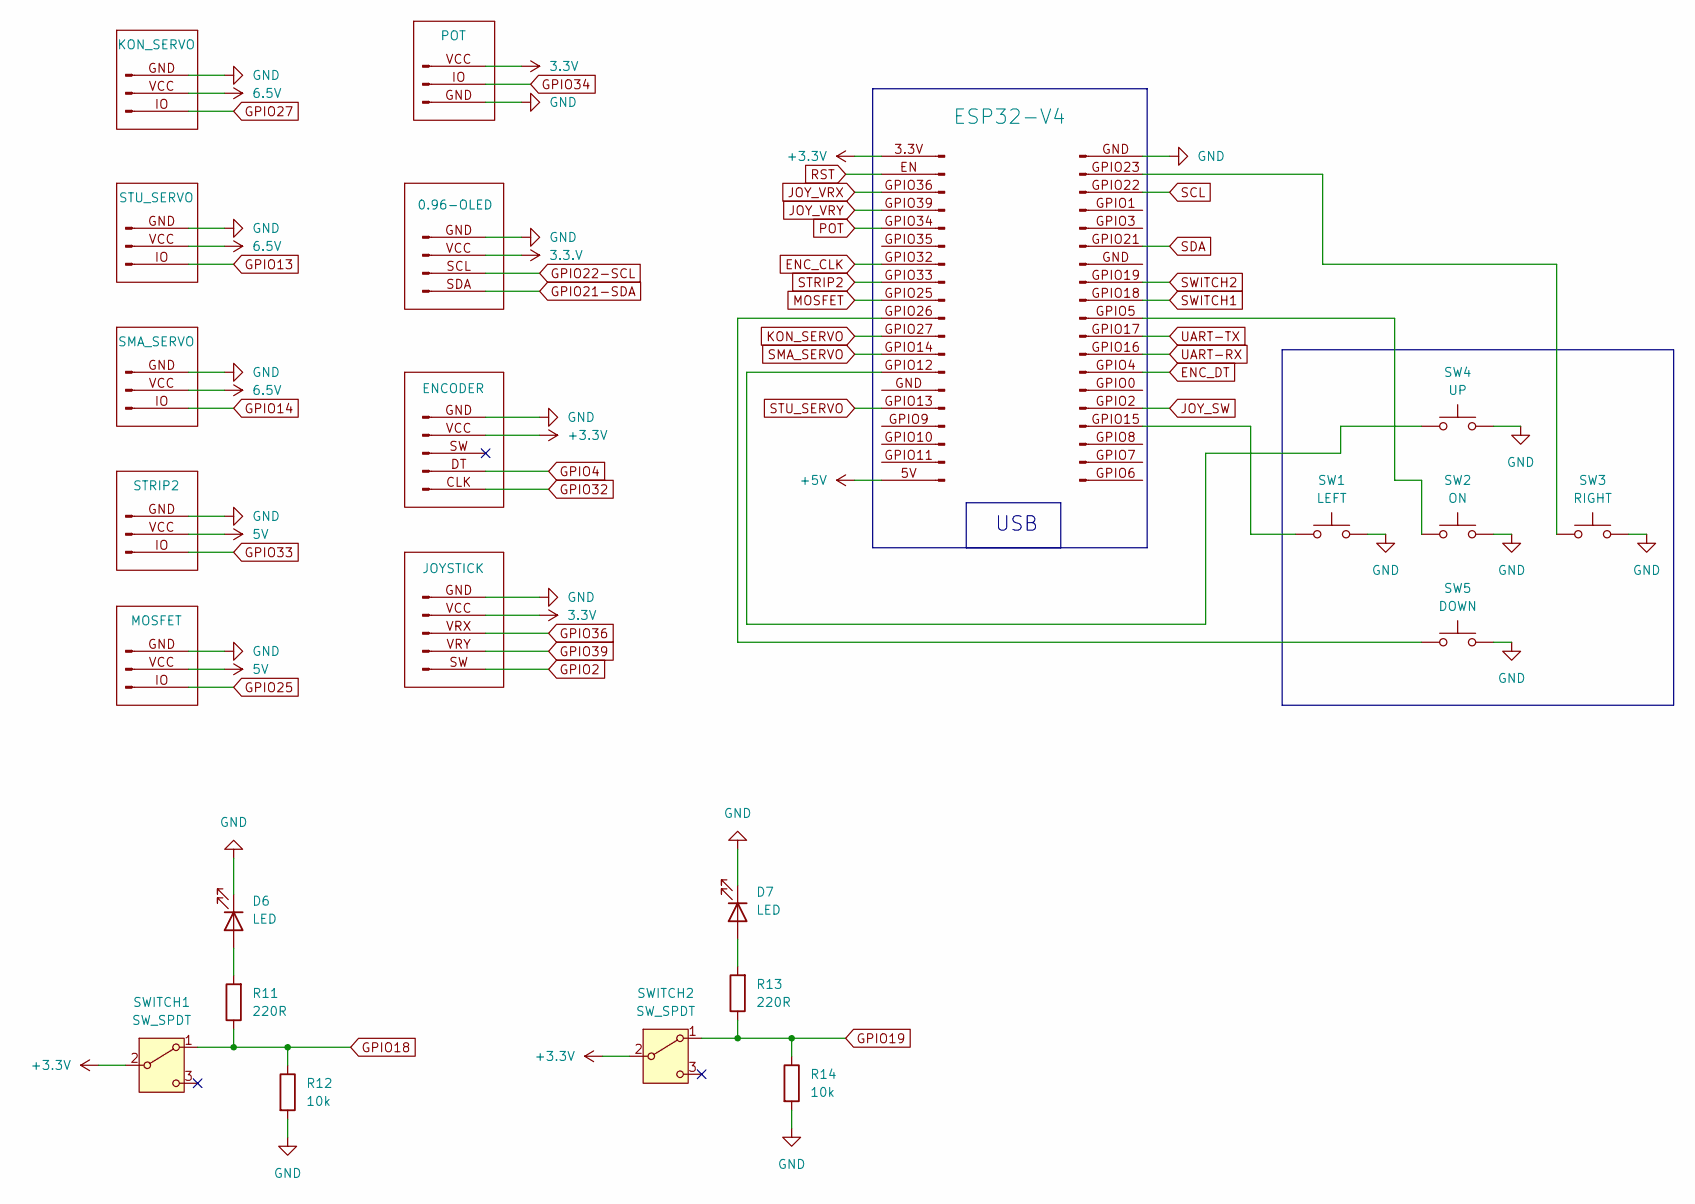
[picture p78: schematic dolni.kicad_sch]

Parts:
0.96-OLED: Conn_01x04_Pin
D6, D7: LED
ENCODER: Conn_01x05_Pin
ESP32-S2, ESP32-V4: Conn_01x22_Pin
JOYSTICK: Conn_01x05_Pin
KON_SERVO: Conn_01x03_Pin
MOSFET: Conn_01x03_Pin
POT: Conn_01x03_Pin
R11, R13: 220R
R12, R14: 10k
SMA_SERVO: Conn_01x03_Pin
STRIP2: Conn_01x03_Pin
STU_SERVO: Conn_01x03_Pin
SW1: LEFT
SW2: ON
SW3: RIGHT
SW4: UP
SW5: DOWN
SWITCH1, SWITCH2: SW_SPDT

Connections:
3.3.V: 0.96-OLED.VCC (Pin_2)
3.3V: JOYSTICK.VCC (Pin_2), POT.VCC (Pin_1)
5V: MOSFET.VCC (Pin_2), STRIP2.VCC (Pin_2)
6.5V: KON_SERVO.VCC (Pin_2), SMA_SERVO.VCC (Pin_2), STU_SERVO.VCC (Pin_2)
+3.3V: ENCODER.VCC (Pin_2), ESP32-S2.3.3V (Pin_1), SWITCH1.2 (B), SWITCH2.2 (B)
+5V: ESP32-S2.5V (Pin_19)
ENC_CLK: ESP32-S2.GPIO32 (Pin_7)
ENC_DT: ESP32-V4.GPIO4 (Pin_13)
GND: 0.96-OLED.GND (Pin_1), D6.1 (K), D7.1 (K), ENCODER.GND (Pin_1), ESP32-V4.GND (Pin_1), JOYSTICK.GND (Pin_1), KON_SERVO.GND (Pin_1), MOSFET.GND (Pin_1), POT.GND (Pin_3), R12.2, R14.2, SMA_SERVO.GND (Pin_1), STRIP2.GND (Pin_1), STU_SERVO.GND (Pin_1), SW1.2, SW2.2, SW3.2, SW4.2, SW5.2
GPIO2: JOYSTICK.SW (Pin_5)
GPIO4: ENCODER.DT (Pin_4)
GPIO13: STU_SERVO.IO (Pin_3)
GPIO14: SMA_SERVO.IO (Pin_3)
GPIO18: R11.1, R12.1, SWITCH1.1 (A)
GPIO19: R13.1, R14.1, SWITCH2.1 (A)
GPIO21-SDA: 0.96-OLED.SDA (Pin_4)
GPIO22-SCL: 0.96-OLED.SCL (SDA)
GPIO25: MOSFET.IO (Pin_3)
GPIO27: KON_SERVO.IO (Pin_3)
GPIO32: ENCODER.CLK (Pin_5)
GPIO33: STRIP2.IO (Pin_3)
GPIO34: POT.IO (Pin_2)
GPIO36: JOYSTICK.VRX (Pin_3)
GPIO39: JOYSTICK.VRY (Pin_4)
JOY_SW: ESP32-V4.GPIO2 (Pin_15)
JOY_VRX: ESP32-S2.GPIO36 (Pin_3)
JOY_VRY: ESP32-S2.GPIO39 (Pin_4)
KON_SERVO: ESP32-S2.GPIO27 (Pin_11)
MOSFET: ESP32-S2.GPIO25 (Pin_9)
unnamed: D6.2 (A), R11.2
unnamed: D7.2 (A), R13.2
unnamed: ESP32-S2.GPIO12 (Pin_13), SW4.1
unnamed: ESP32-S2.GPIO26 (Pin_10), SW5.1
unnamed: ESP32-V4.GPIO5 (Pin_10), SW2.1
unnamed: ESP32-V4.GPIO15 (Pin_16), SW1.1
unnamed: ESP32-V4.GPIO23 (Pin_2), SW3.1
POT: ESP32-S2.GPIO34 (Pin_5)
RST: ESP32-S2.EN (Pin_2)
SCL: ESP32-V4.GPIO22 (GPIO44)
SDA: ESP32-V4.GPIO21 (Pin_6)
SMA_SERVO: ESP32-S2.GPIO14 (Pin_12)
STRIP2: ESP32-S2.GPIO33 (GPIO15)
STU_SERVO: ESP32-S2.GPIO13 (Pin_15)
SWITCH1: ESP32-V4.GPIO18 (Pin_9)
SWITCH2: ESP32-V4.GPIO19 (Pin_8)
UART-RX: ESP32-V4.GPIO16 (Pin_12)
UART-TX: ESP32-V4.GPIO17 (Pin_11)

Notes on the sheet:
USB
