ZemanNz/ESP-Demo-Box/documentation/zapojeni/horni.kicad_sch

## KiCad design documentation/zapojeni/horni.kicad_sch (2026-09-20)

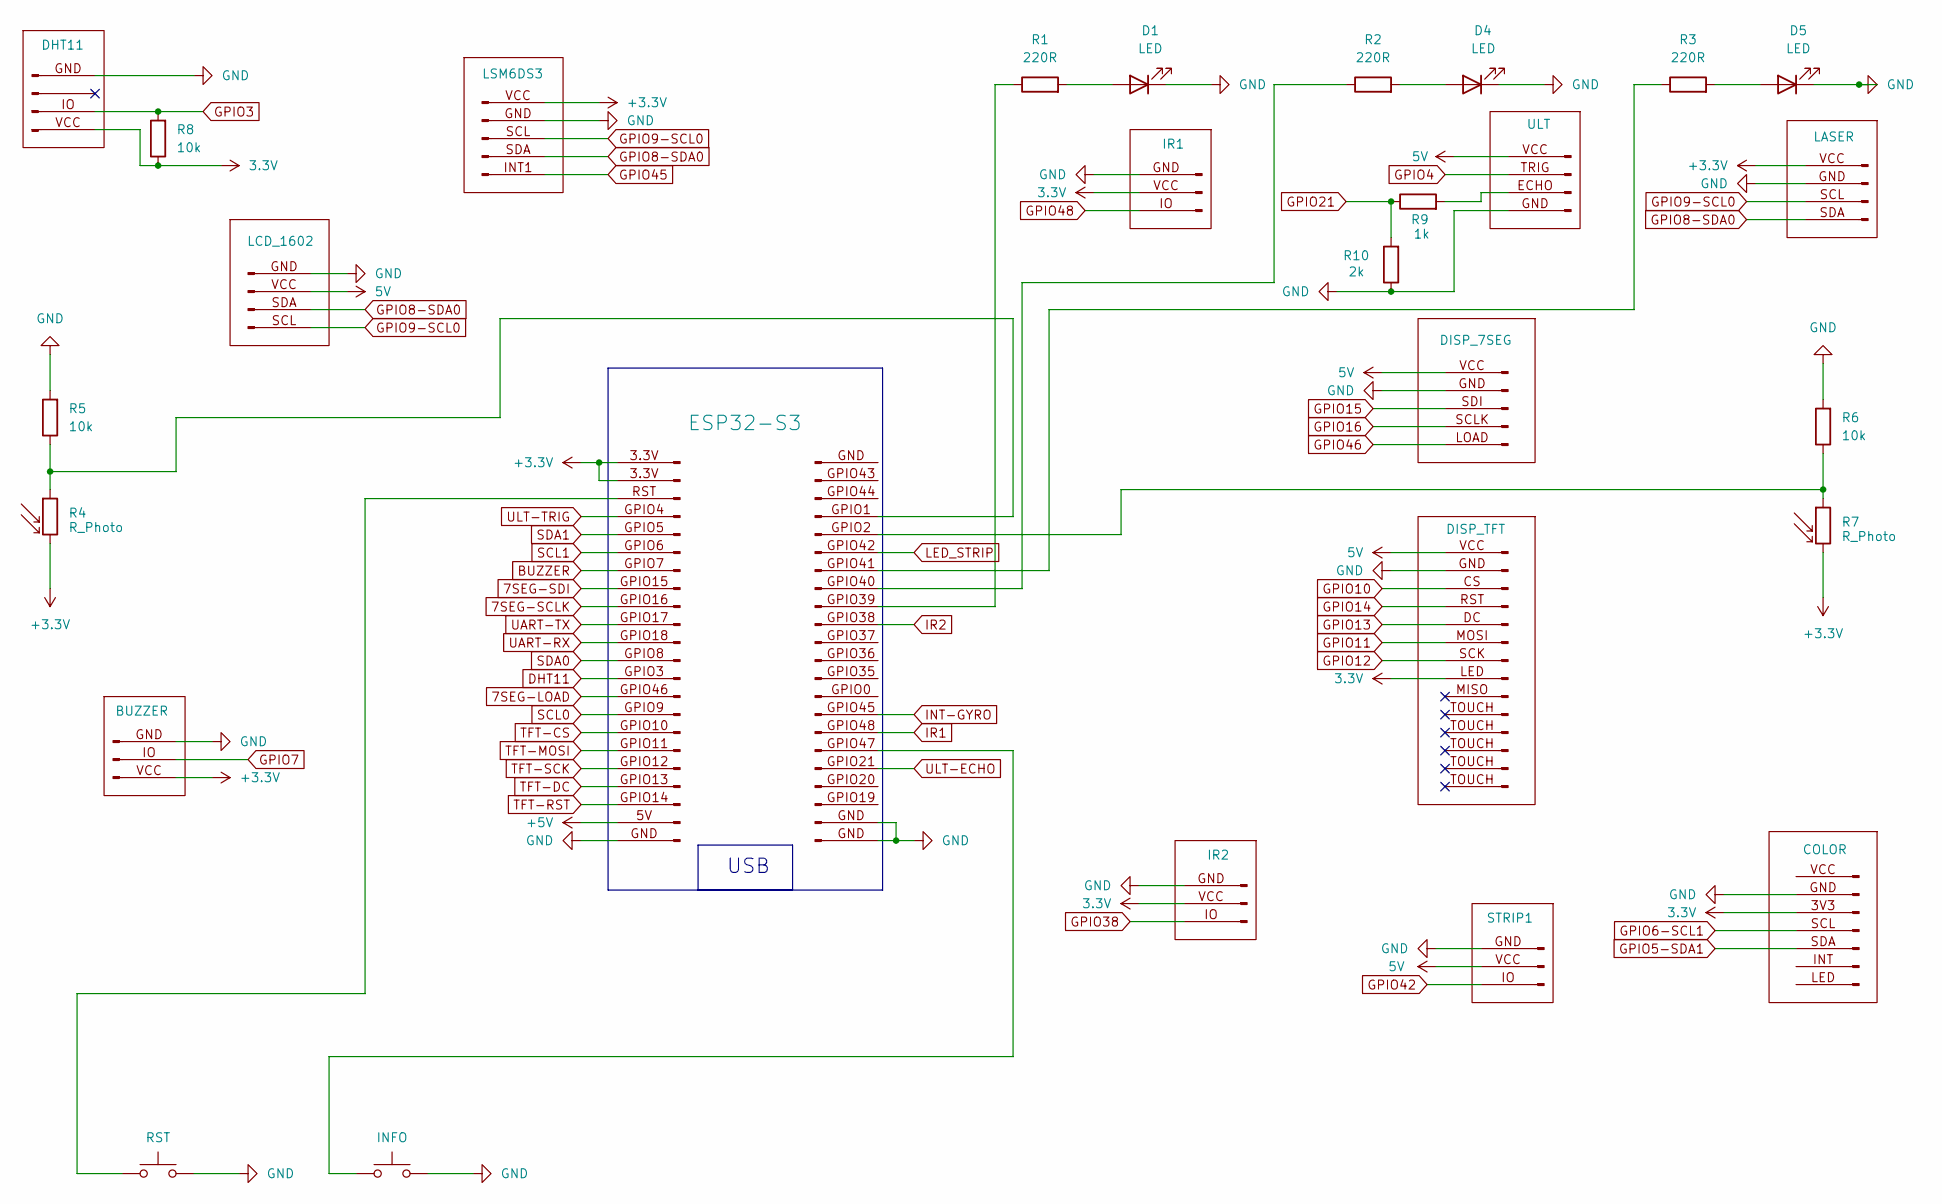
[picture p79: schematic horni.kicad_sch]

Parts:
BUZZER: Conn_01x03_Pin
COLOR: Conn_01x07_Pin
D1, D4, D5: LED
DHT11: Conn_01x03_Pin
DISP_7SEG: Conn_01x05_Pin
DISP_TFT: Conn_01x14_Pin
ESP32-S1, ESP32-S3: Conn_01x22_Pin
INFO: SW_Push
IR1, IR2: Conn_01x03_Pin
LASER: Conn_01x04_Pin
LCD_1602: Conn_01x04_Pin
LSM6DS3: Conn_01x05_Pin
R1, R2, R3: 220R
R4, R7: R_Photo
R5, R6, R8: 10k
R9: 1k
R10: 2k
RST: SW_Push
STRIP1: Conn_01x03_Pin
ULT: Conn_01x04_Pin

Connections:
3.3V: COLOR.3V3 (Pin_3), DHT11.VCC (Pin_3), DISP_TFT.LED (Pin_8), IR1.VCC (Pin_2), IR2.VCC (Pin_2), R8.1
5V: DISP_7SEG.VCC (Pin_1), DISP_TFT.VCC (Pin_1), LCD_1602.VCC (Pin_2), STRIP1.VCC (Pin_2), ULT.VCC (Pin_1)
7SEG-LOAD: ESP32-S1.GPIO46 (Pin_14)
7SEG-SCLK: ESP32-S1.GPIO16 (Pin_9)
7SEG-SDI: ESP32-S1.GPIO15
+3.3V: BUZZER.VCC (Pin_3), ESP32-S1.3.3V (Pin_1), LASER.VCC (Pin_1), LSM6DS3.VCC (Pin_1), R4.2, R7.2
+5V: ESP32-S1.5V (Pin_21)
BUZZER: ESP32-S1.GPIO7 (Pin_7)
DHT11: ESP32-S1.GPIO3 (Pin_13)
GND: BUZZER.GND (Pin_1), COLOR.GND (Pin_2), D1.1 (K), D4.1 (K), D5.1 (K), DHT11.GND (Pin_1), DISP_7SEG.GND (Pin_2), DISP_TFT.GND (Pin_2), ESP32-S1.GND (Pin_22), ESP32-S3.GND (Pin_1), INFO.2, IR1.GND (Pin_1), IR2.GND (Pin_1), LASER.GND (Pin_2), LCD_1602.GND (Pin_1), LSM6DS3.GND (Pin_2), R5.2, R6.2, R10.1, RST.2, STRIP1.GND (Pin_1), ULT.GND (Pin_4)
GPIO3: DHT11.IO (Pin_3), R8.2
GPIO4: ULT.TRIG (Pin_2)
GPIO5-SDA1: COLOR.SDA (Pin_5)
GPIO6-SCL1: COLOR.SCL (SDA)
GPIO7: BUZZER.IO (Pin_2)
GPIO8-SDA0: LASER.SDA (Pin_4), LCD_1602.SDA, LSM6DS3.SDA (Pin_4)
GPIO9-SCL0: LASER.SCL (SDA), LCD_1602.SCL (Pin_4), LSM6DS3.SCL (Pin_3)
GPIO10: DISP_TFT.CS (Pin_3)
GPIO11: DISP_TFT.MOSI (Pin_6)
GPIO12: DISP_TFT.SCK (Pin_7)
GPIO13: DISP_TFT.DC (Pin_5)
GPIO14: DISP_TFT.RST (Pin_4)
GPIO15: DISP_7SEG.SDI (Pin_3)
GPIO16: DISP_7SEG.SCLK (Pin_4)
GPIO21: R9.1, R10.2
GPIO38: IR2.IO (Pin_3)
GPIO42: STRIP1.IO (Pin_3)
GPIO45: LSM6DS3.INT1 (Pin_5)
GPIO46: DISP_7SEG.LOAD (Pin_5)
GPIO48: IR1.IO (Pin_3)
INT-GYRO: ESP32-S3.GPIO45 (Pin_15)
IR1: ESP32-S3.GPIO48 (Pin_16)
IR2: ESP32-S3.GPIO38 (Pin_10)
LED_STRIP: ESP32-S3.GPIO42 (Pin_6)
unnamed: D1.2 (A), R1.2
unnamed: D4.2 (A), R2.2
unnamed: D5.2 (A), R3.2
unnamed: ESP32-S1.RST (Pin_3), RST.1
unnamed: ESP32-S3.GPIO1 (Pin_4), R4.1, R5.1
unnamed: ESP32-S3.GPIO2 (Pin_5), R6.1, R7.1
unnamed: ESP32-S3.GPIO39 (Pin_9), R1.1
unnamed: ESP32-S3.GPIO40 (Pin_8), R2.1
unnamed: ESP32-S3.GPIO41 (Pin_7), R3.1
unnamed: ESP32-S3.GPIO47 (Pin_17), INFO.1
unnamed: R9.2, ULT.ECHO (Pin_3)
SCL0: ESP32-S1.GPIO9 (Pin_15)
SCL1: ESP32-S1.GPIO6 (Pin_6)
SDA0: ESP32-S1.GPIO8 (Pin_12)
SDA1: ESP32-S1.GPIO5 (Pin_5)
TFT-CS: ESP32-S1.GPIO10 (Pin_16)
TFT-DC: ESP32-S1.GPIO13 (Pin_19)
TFT-MOSI: ESP32-S1.GPIO11 (Pin_17)
TFT-RST: ESP32-S1.GPIO14 (Pin_20)
TFT-SCK: ESP32-S1.GPIO12 (Pin_18)
UART-RX: ESP32-S1.GPIO18 (Pin_11)
UART-TX: ESP32-S1.GPIO17 (Pin_10)
ULT-ECHO: ESP32-S3.GPIO21 (Pin_18)
ULT-TRIG: ESP32-S1.GPIO4 (Pin_4)

Notes on the sheet:
USB
