ZemanNz/ESP-Demo-Box/documentation/zapojeni/zapojeni.kicad_sch

## KiCad design documentation/zapojeni/zapojeni.kicad_sch (2026-09-20)

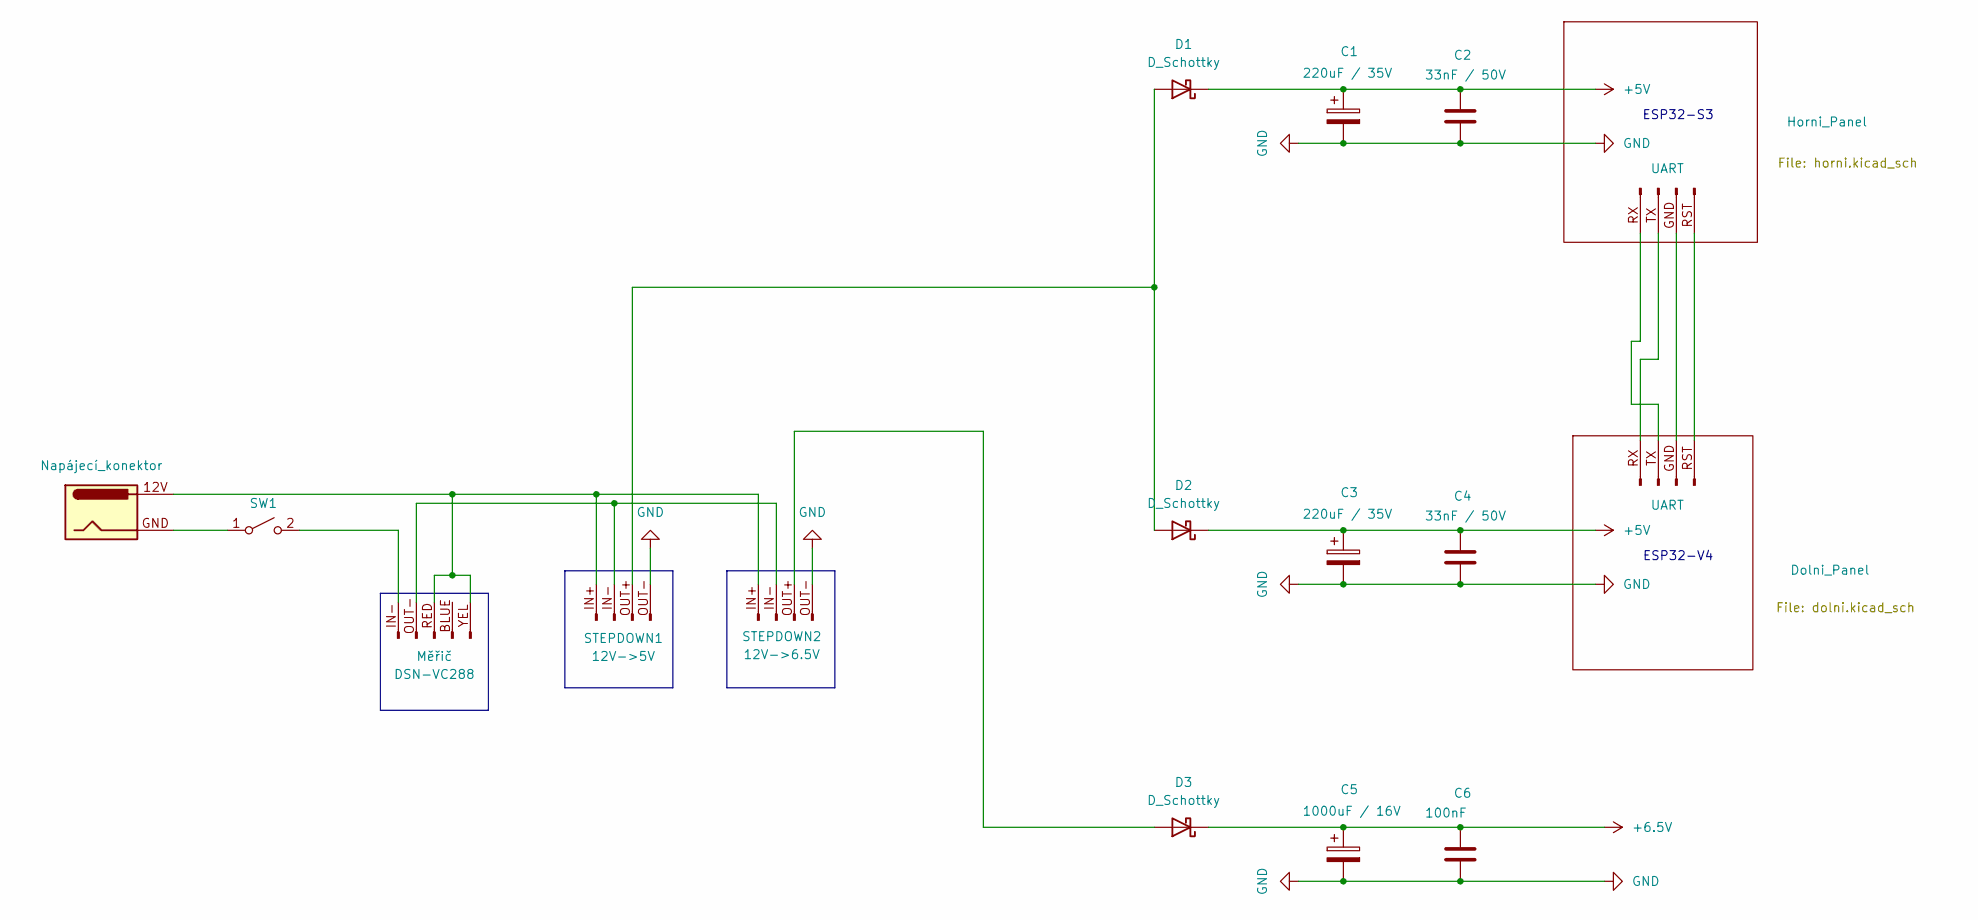
[picture p80: schematic zapojeni.kicad_sch]

Parts:
C1, C3: 220uF / 35V
C2, C4: 33nF / 50V
C5: 1000uF / 16V
C6: 100nF
D1, D2, D3: D_Schottky
J1, J2: UART
Měřič: DSN-VC288
Napájecí_konektor: (no value)
STEPDOWN1: 12V->5V
STEPDOWN2: 12V->6.5V
SW1: SW_SPST

Connections:
+5V: C1.1, C2.1, C3.1, C4.1, D1.1 (K), D2.1 (K)
+6.5V: C5.1, C6.1, D3.1 (K)
GND: C1.2, C2.2, C3.2, C4.2, C5.2, C6.2, STEPDOWN1.OUT- (Pin_4), STEPDOWN2.OUT- (Pin_4)
unnamed: D1.2 (A), D2.2 (A), STEPDOWN1.OUT+ (Pin_3)
unnamed: D3.2 (A), STEPDOWN2.OUT+ (Pin_3)
unnamed: J1.GND (Pin_2), J2.GND (Pin_2)
unnamed: J1.RST (Pin_1), J2.RST (Pin_1)
unnamed: J1.RX (Pin_4), J2.TX (Pin_3)
unnamed: J1.TX (Pin_3), J2.RX (Pin_4)
unnamed: Měřič.IN-, SW1.2 (B)
unnamed: Měřič.OUT-, STEPDOWN1.IN-, STEPDOWN2.IN-
unnamed: Měřič.RED (Pin_3), Měřič.YEL, Napájecí_konektor.12V, STEPDOWN1.IN+, STEPDOWN2.IN+
unnamed: Napájecí_konektor.GND, SW1.1 (A)

Notes on the sheet:
ESP32-V4
ESP32-S3
